MrDoritos/Wearable/dpad.png

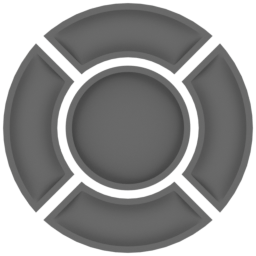
dpad.png
