MrDoritos/Wearable/dpad_arrow.png

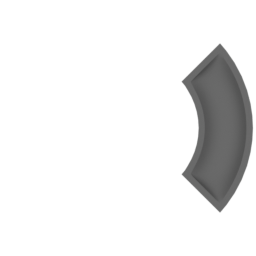
dpad_arrow.png
