MrDoritos/Wearable/dpad_enter.png

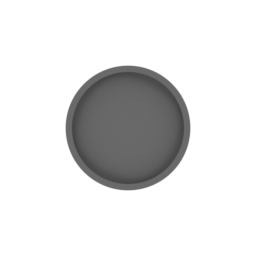
dpad_enter.png
