MrDoritos/Wearable/font.png

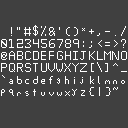
font.png
