MrDoritos/Wearable/fonts/fixedsys-excelsior-301.ttf_8x8.png

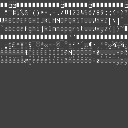
fonts/fixedsys-excelsior-301.ttf_8x8.png
