MrDoritos/Wearable/fonts/fixedsys-excelsior-301.ttf_8x14_fixed.png

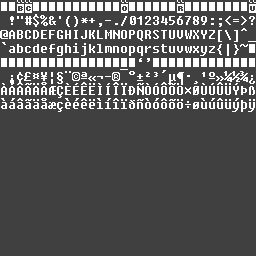
fonts/fixedsys-excelsior-301.ttf_8x14_fixed.png
