MrDoritos/Wearable/fonts/fixedsys-excelsior-301.ttf_12x12.png

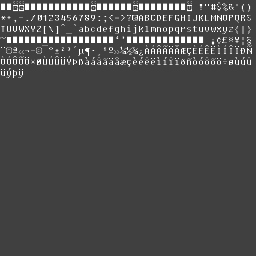
fonts/fixedsys-excelsior-301.ttf_12x12.png
