MrDoritos/Wearable/fonts/fixedsys-excelsior-301.ttf_12x16.png

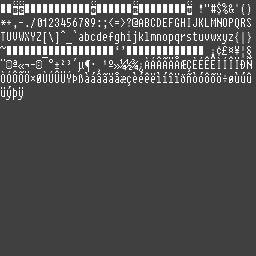
fonts/fixedsys-excelsior-301.ttf_12x16.png
