MrDoritos/Wearable/fonts/fixedsys-excelsior-301.ttf_14x16.png

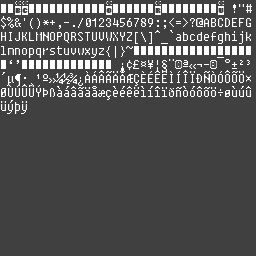
fonts/fixedsys-excelsior-301.ttf_14x16.png
