MrDoritos/Wearable/fonts/fixedsys-excelsior-301.ttf_16x16.png

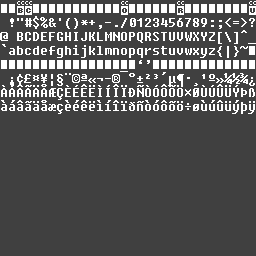
fonts/fixedsys-excelsior-301.ttf_16x16.png
