MrDoritos/Wearable/fonts/Perfect DOS VGA 437 Win.ttf_12x12.png

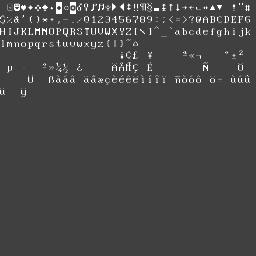
fonts/Perfect DOS VGA 437 Win.ttf_12x12.png
