MrDoritos/Wearable/fonts/Perfect DOS VGA 437 Win.ttf_16x16.png

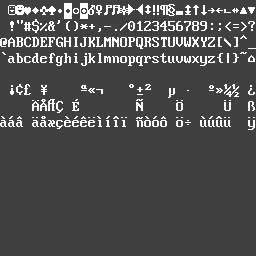
fonts/Perfect DOS VGA 437 Win.ttf_16x16.png
