MrDoritos/Wearable/fonts/Px437_DOS-V_re_JPN12.ttf_8x12.png

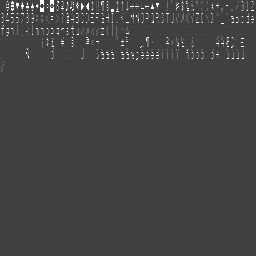
fonts/Px437_DOS-V_re_JPN12.ttf_8x12.png
