MrDoritos/Wearable/fonts/Px437_IBM_BIOS.ttf_7x7.png

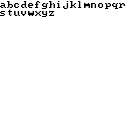
fonts/Px437_IBM_BIOS.ttf_7x7.png
