MrDoritos/Wearable/fonts/Px437_IBM_BIOS.ttf_8x12.png

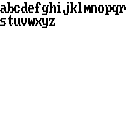
fonts/Px437_IBM_BIOS.ttf_8x12.png
