MrDoritos/Wearable/fonts/Px437_IBM_CGAthin.ttf_8x8.png

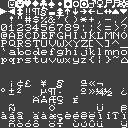
fonts/Px437_IBM_CGAthin.ttf_8x8.png
