MrDoritos/Wearable/fonts/Px437_IBM_Model3x_Alt1.ttf_8x16.png

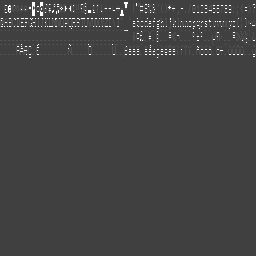
fonts/Px437_IBM_Model3x_Alt1.ttf_8x16.png
