MrDoritos/Wearable/fonts/Px437_IBM_Model3x_Alt1.ttf_16x16.png

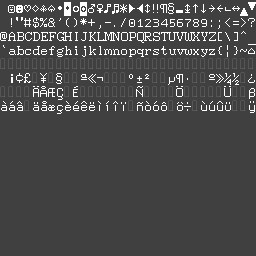
fonts/Px437_IBM_Model3x_Alt1.ttf_16x16.png
