MrDoritos/Wearable/fonts/Px437_IBM_VGA_9x16.ttf_8x16.png

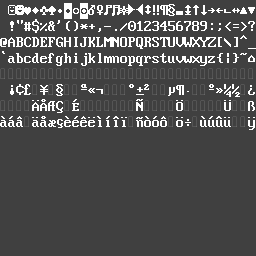
fonts/Px437_IBM_VGA_9x16.ttf_8x16.png
