MrDoritos/Wearable/fonts/raster.ttf_6x12.png

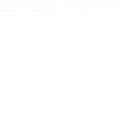
fonts/raster.ttf_6x12.png
