MrDoritos/Wearable/fonts/raster.ttf_8x8.png

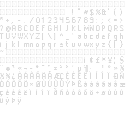
fonts/raster.ttf_8x8.png
