MrDoritos/Wearable/fonts/raster.ttf_12x16.png

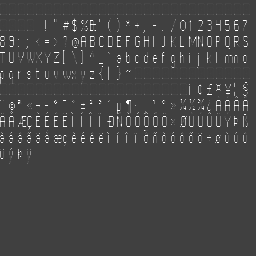
fonts/raster.ttf_12x16.png
