MrDoritos/Wearable/fonts/raster.ttf_16x12.png

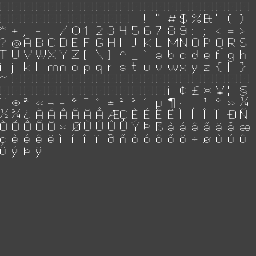
fonts/raster.ttf_16x12.png
