MrDoritos/Wearable/fonts/raster.ttf_16x16.png

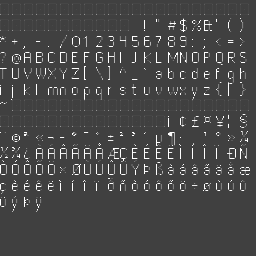
fonts/raster.ttf_16x16.png
