MrDoritos/Wearable/fonts/raster.ttf_20x16.png

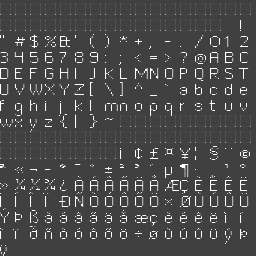
fonts/raster.ttf_20x16.png
