MrDoritos/Wearable/fonts/raster.ttf_24x16.png

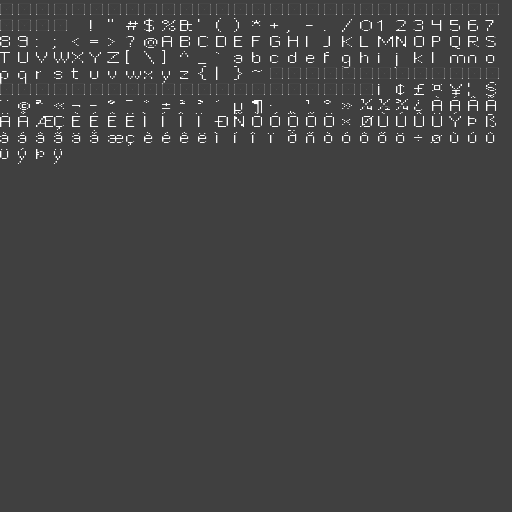
fonts/raster.ttf_24x16.png
