MrDoritos/Wearable/layout3.png

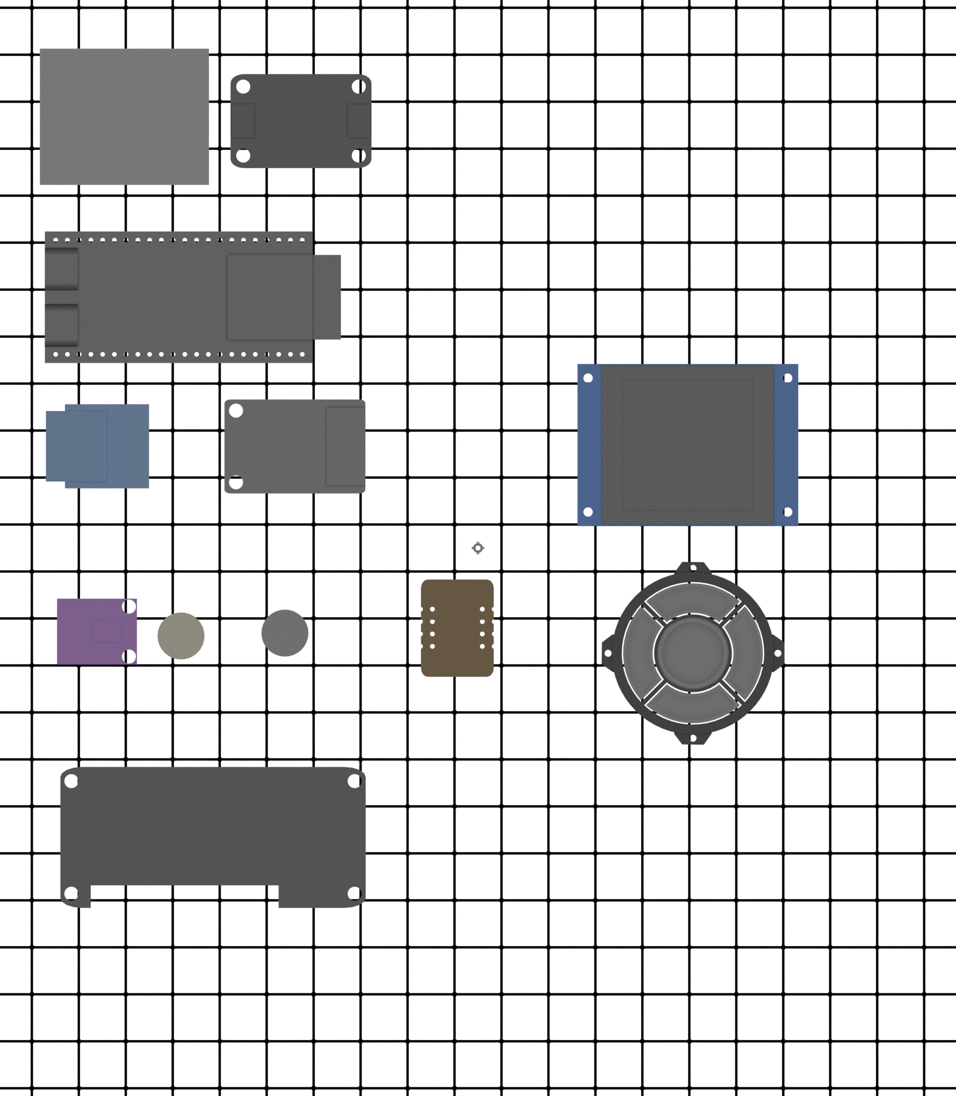
layout3.png
