MrDoritos/Wearable/layout.png

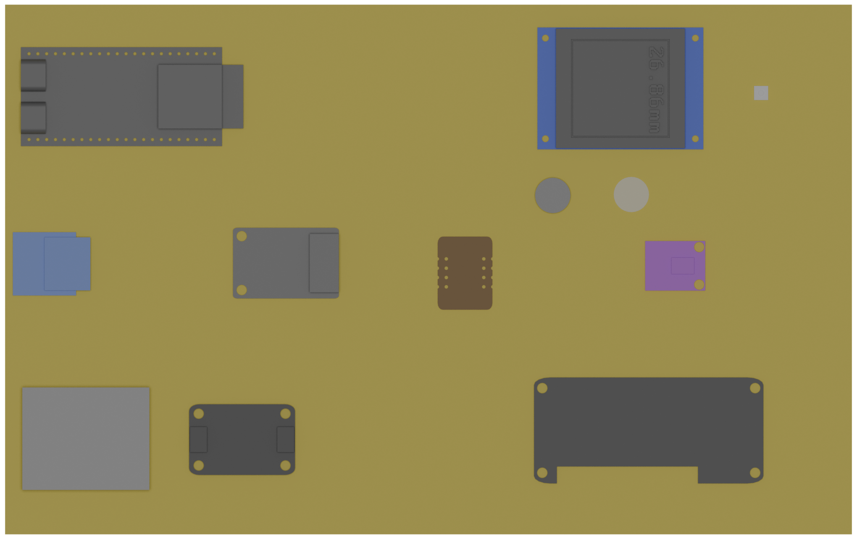
layout.png
