MrDoritos/Wearable/Pics/51+UH7-mXzL._SL1100_.jpg

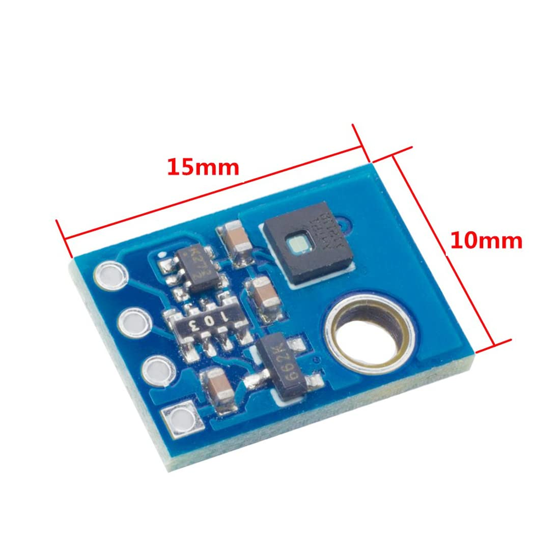
Pics/51+UH7-mXzL._SL1100_.jpg
