MrDoritos/Wearable/Pics/51AXbPtVahL._SL1200_.jpg

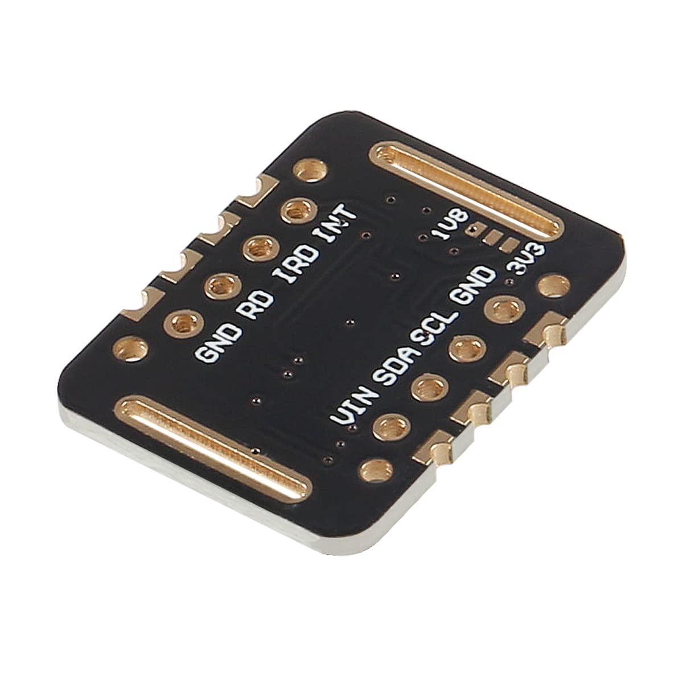
Pics/51AXbPtVahL._SL1200_.jpg
