MrDoritos/Wearable/Pics/51Op+VarA2L._SL1100_.jpg

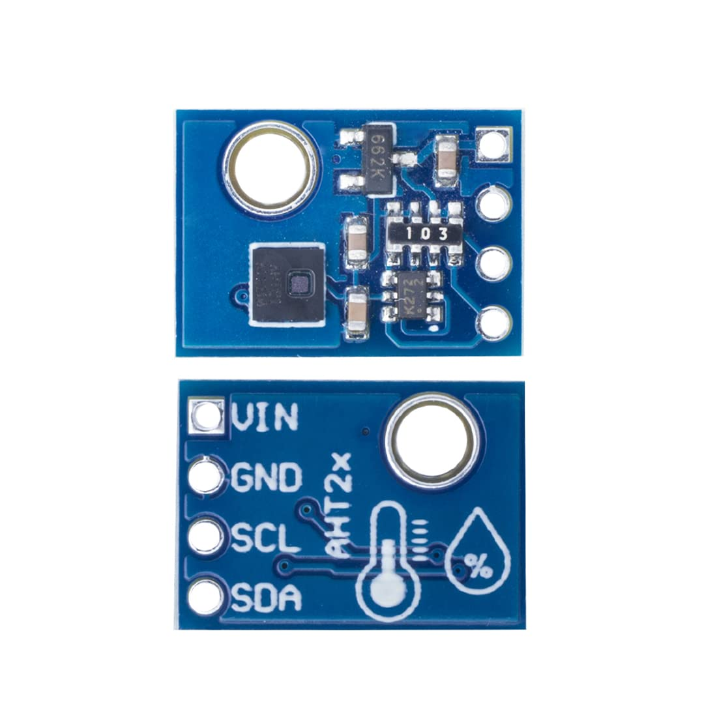
Pics/51Op+VarA2L._SL1100_.jpg
