MrDoritos/Wearable/Pics/51P6r7VXNBL._SL1000_.jpg

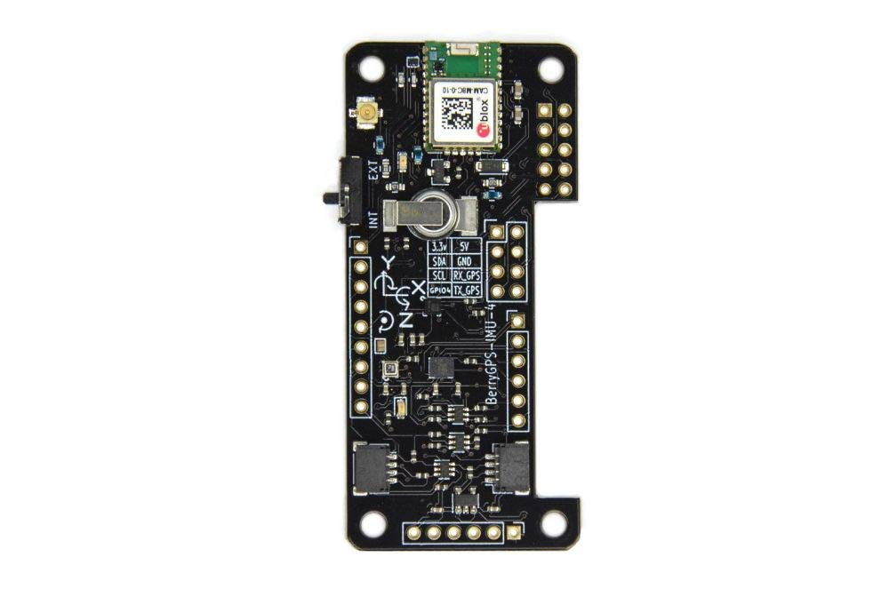
Pics/51P6r7VXNBL._SL1000_.jpg
