MrDoritos/Wearable/Pics/51W31oze62L._SL1200_.jpg

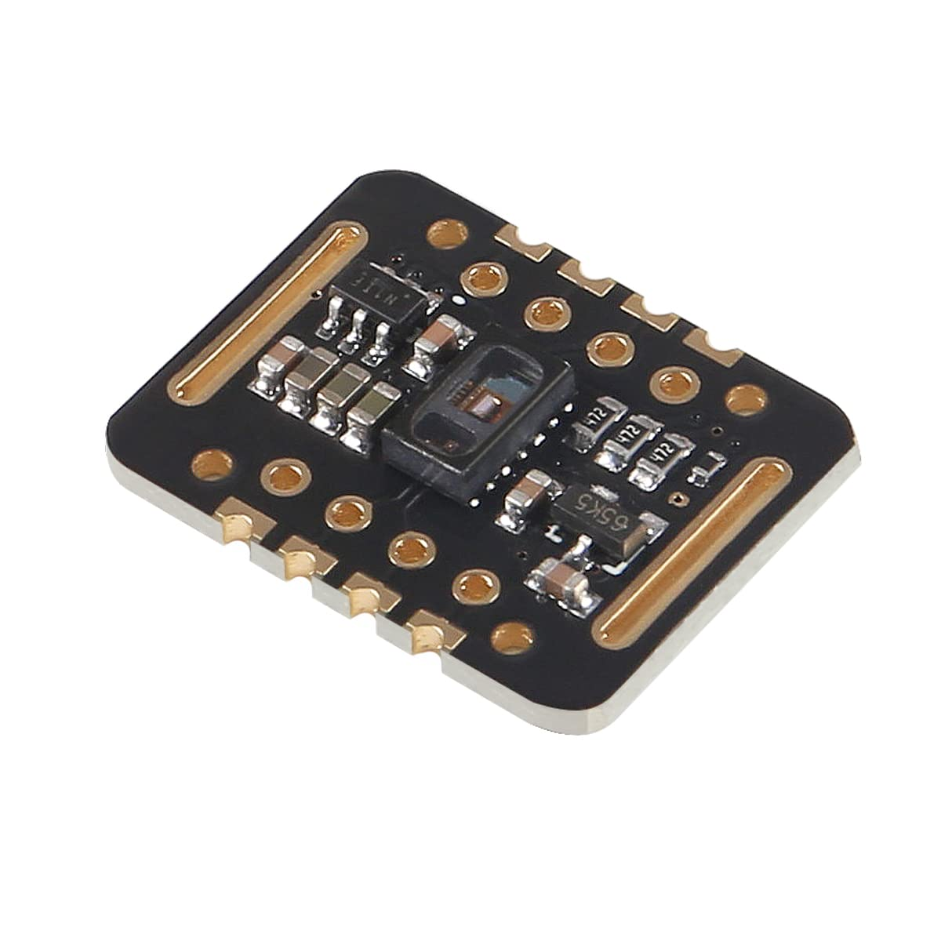
Pics/51W31oze62L._SL1200_.jpg
