MrDoritos/Wearable/Pics/51ZjLzfTUjL.jpg

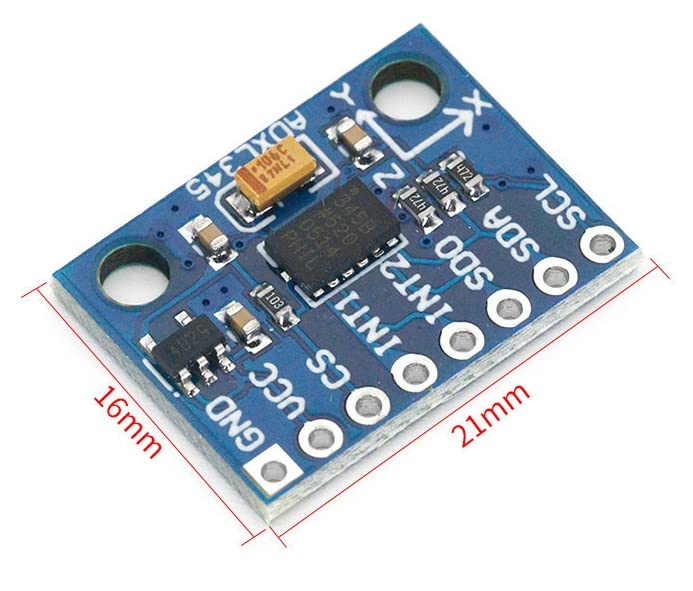
Pics/51ZjLzfTUjL.jpg
