MrDoritos/Wearable/Pics/61DWyjEP5hL._AC_SL1000_.jpg

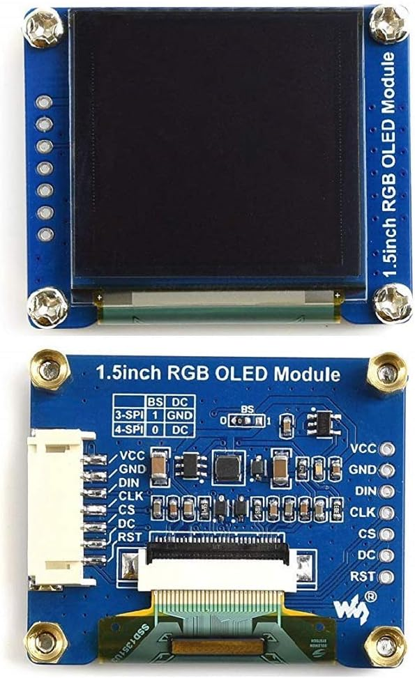
Pics/61DWyjEP5hL._AC_SL1000_.jpg
