MrDoritos/Wearable/Pics/61G-zMD8dRL._SL1000_.jpg

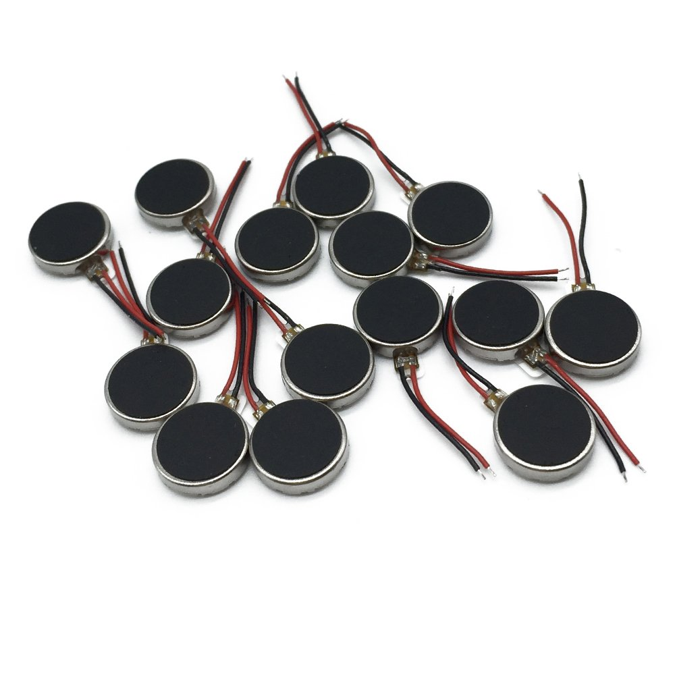
Pics/61G-zMD8dRL._SL1000_.jpg
