MrDoritos/Wearable/Pics/61ibA389aeL._AC_SL1500_.jpg

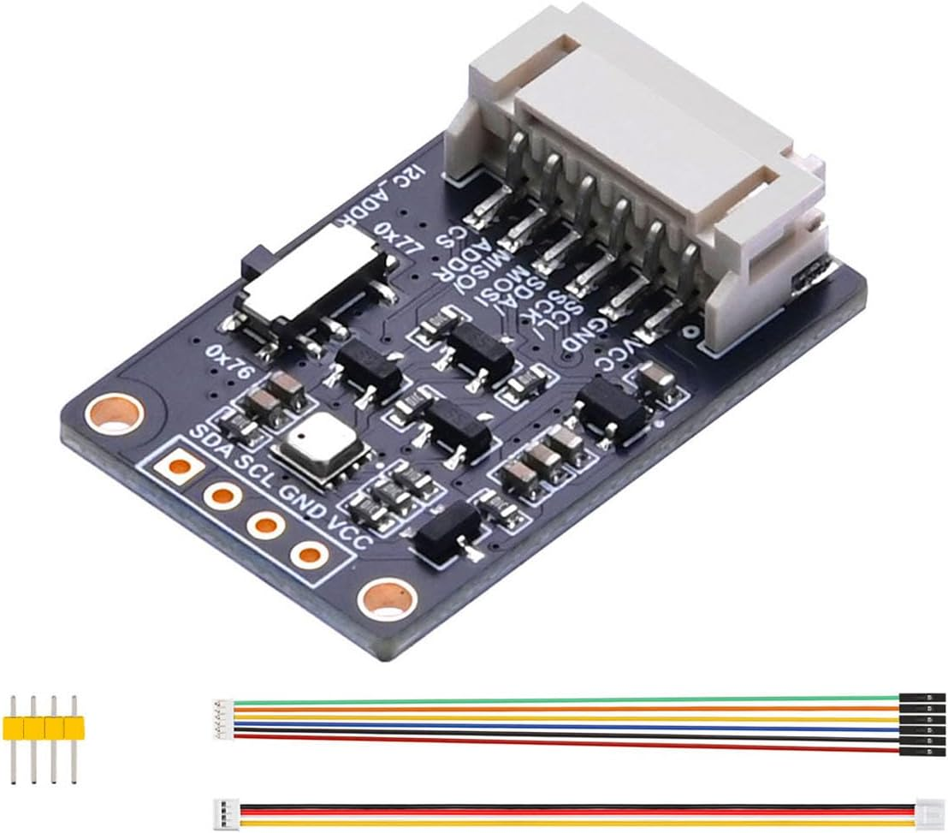
Pics/61ibA389aeL._AC_SL1500_.jpg
