MrDoritos/Wearable/Pics/61LNeiGi+DL._SL1200_.jpg

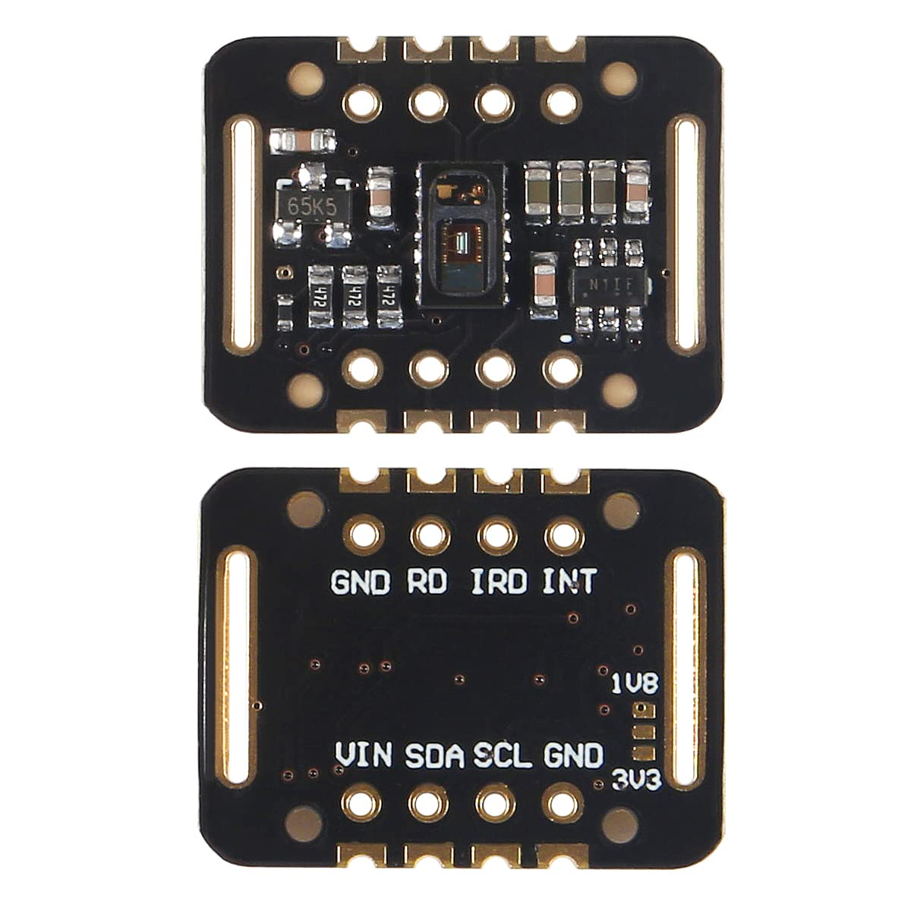
Pics/61LNeiGi+DL._SL1200_.jpg
