MrDoritos/Wearable/Pics/61Ofmry2-IL._SL1000_.jpg

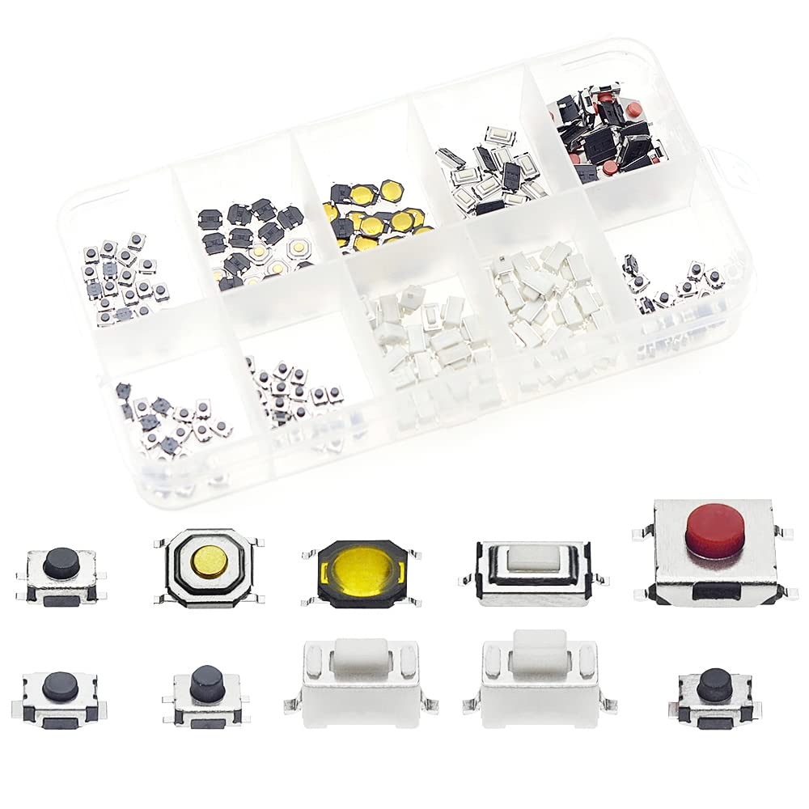
Pics/61Ofmry2-IL._SL1000_.jpg
