MrDoritos/Wearable/Pics/61Oh5a2cU0L._AC_SL1200_.jpg

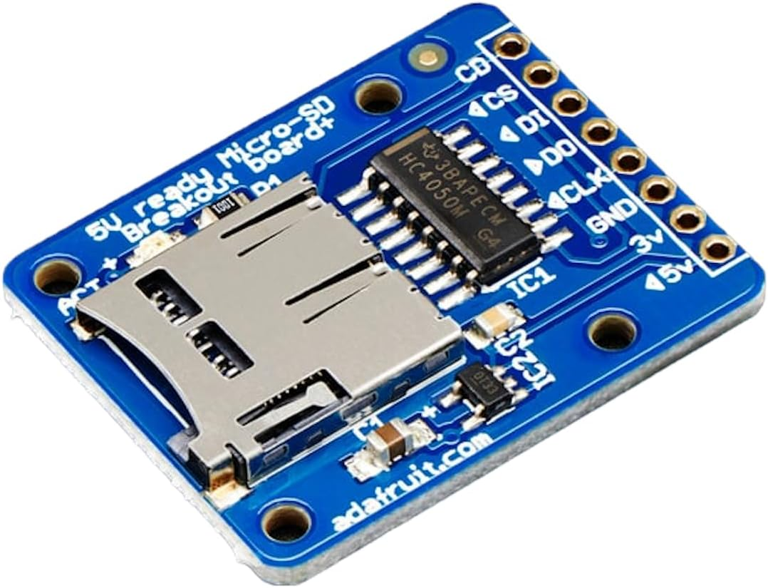
Pics/61Oh5a2cU0L._AC_SL1200_.jpg
