MrDoritos/Wearable/Pics/61qT42ub8qL._SL1200_.jpg

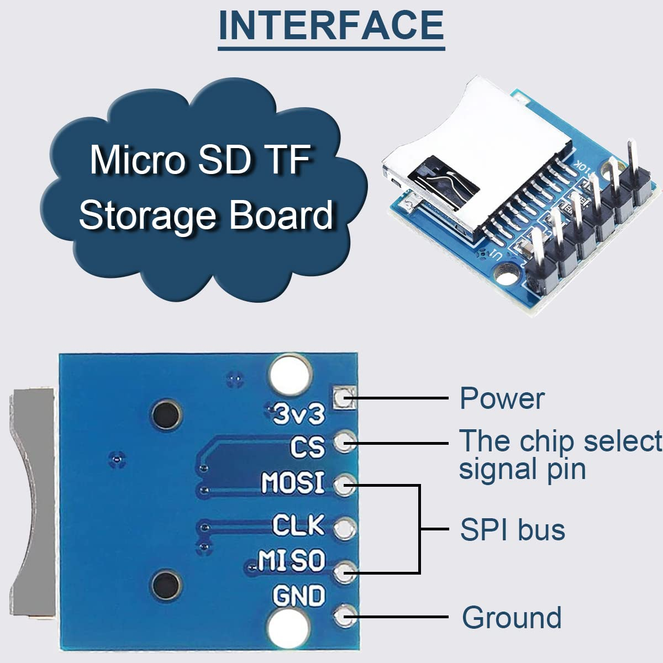
Pics/61qT42ub8qL._SL1200_.jpg
