MrDoritos/Wearable/Pics/61SEPn4aGYL._SL1100_.jpg

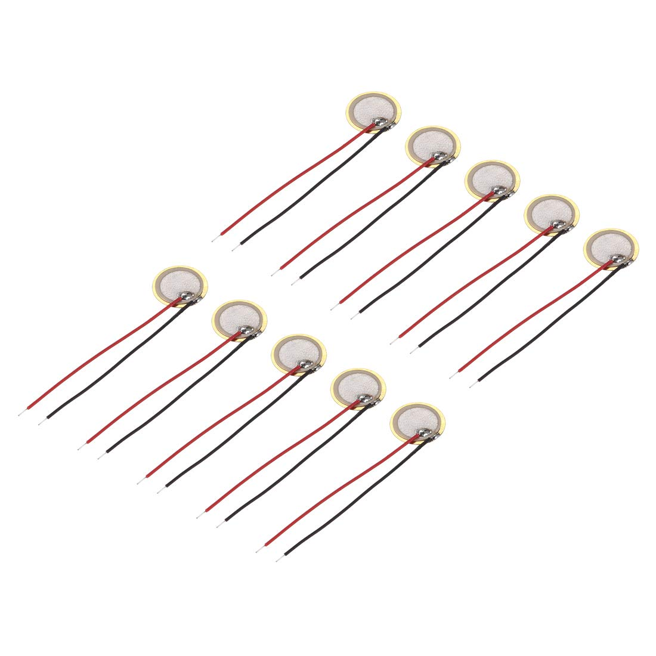
Pics/61SEPn4aGYL._SL1100_.jpg
