MrDoritos/Wearable/Pics/61SvwQWat1L._AC_SL1500_.jpg

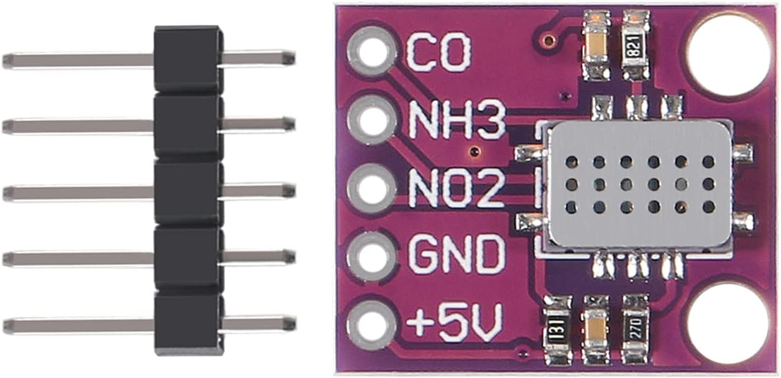
Pics/61SvwQWat1L._AC_SL1500_.jpg
