MrDoritos/Wearable/Pics/71bgBU8mavL._AC_SL1500_.jpg

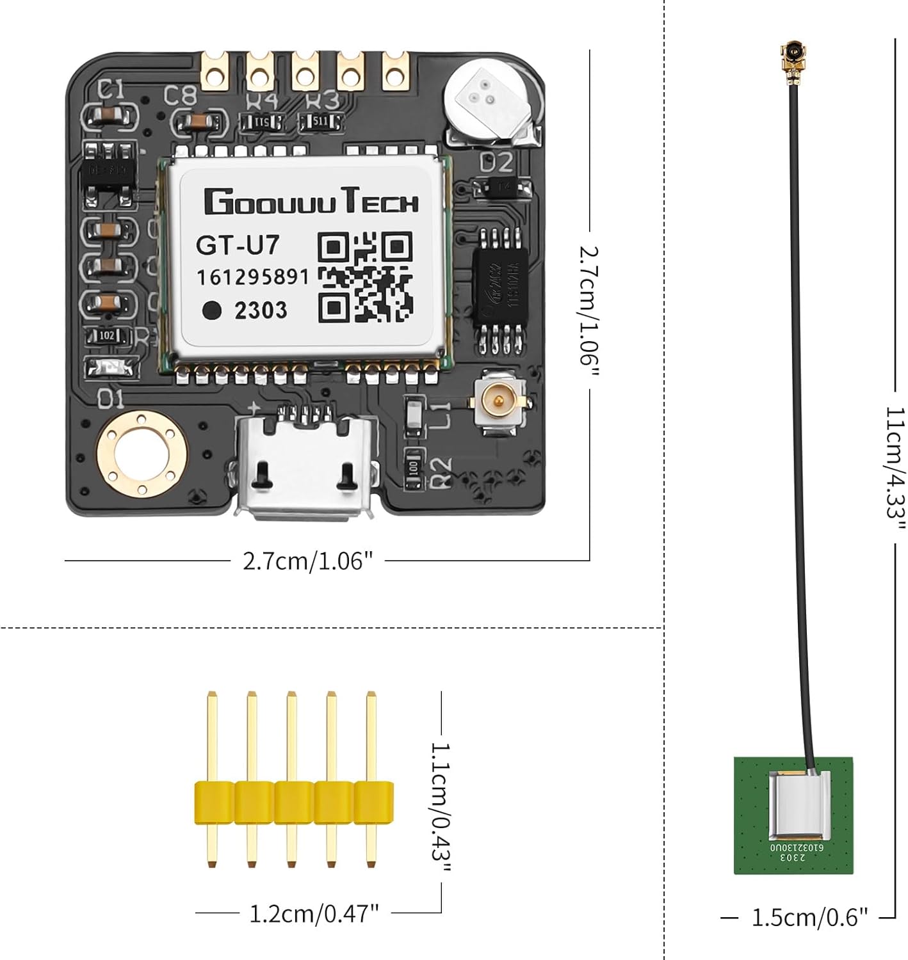
Pics/71bgBU8mavL._AC_SL1500_.jpg
