MrDoritos/Wearable/Pics/71tm7mbUd7L._AC_SL1500_.jpg

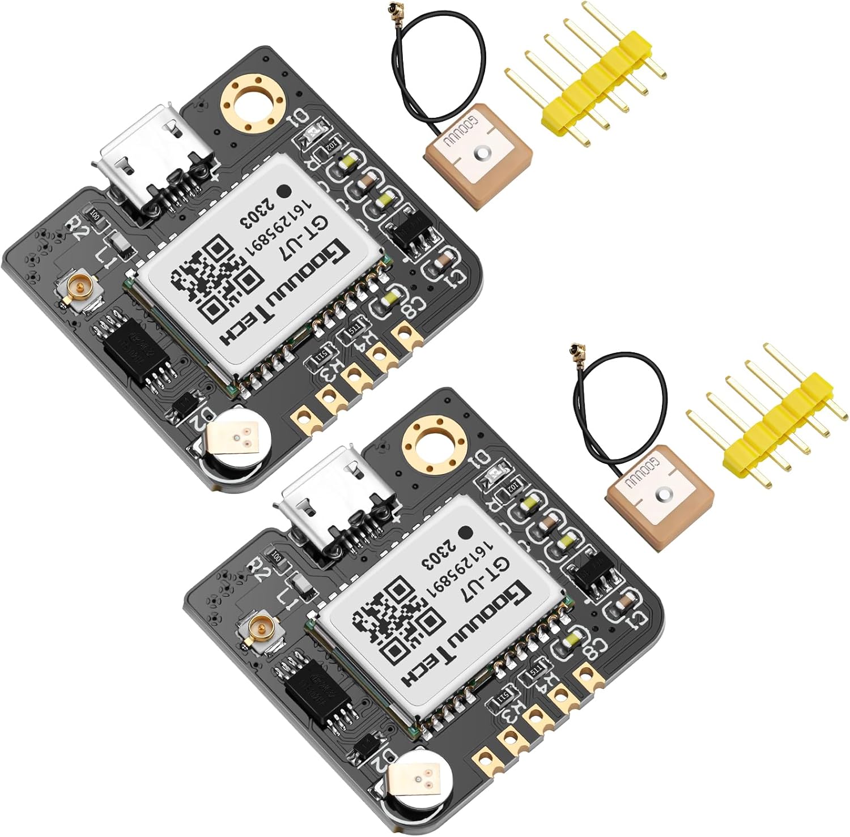
Pics/71tm7mbUd7L._AC_SL1500_.jpg
