MrDoritos/Wearable/Pics/71tysou55pL._SL1500_.jpg

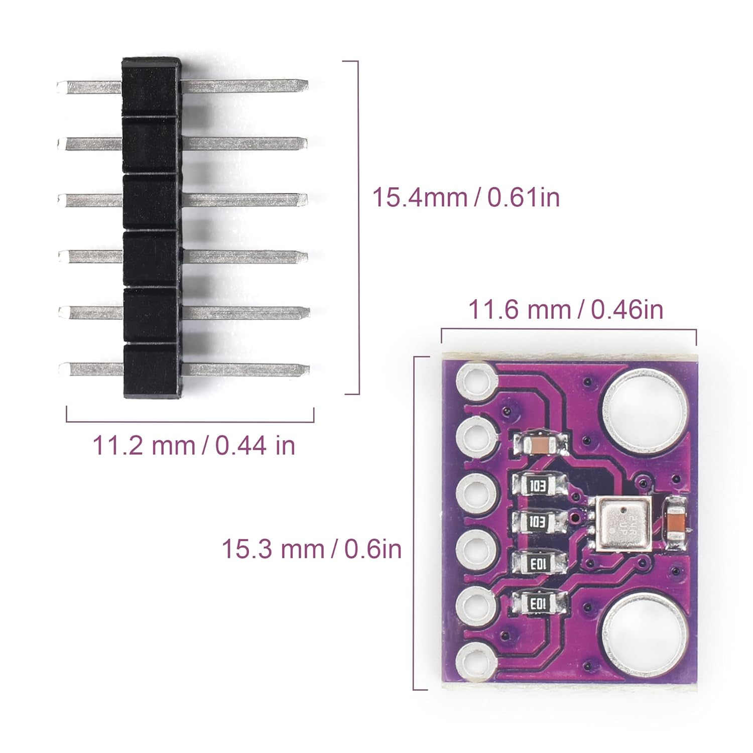
Pics/71tysou55pL._SL1500_.jpg
