MrDoritos/Wearable/Pics/71Z4uBD5LkL._SL1500_.jpg

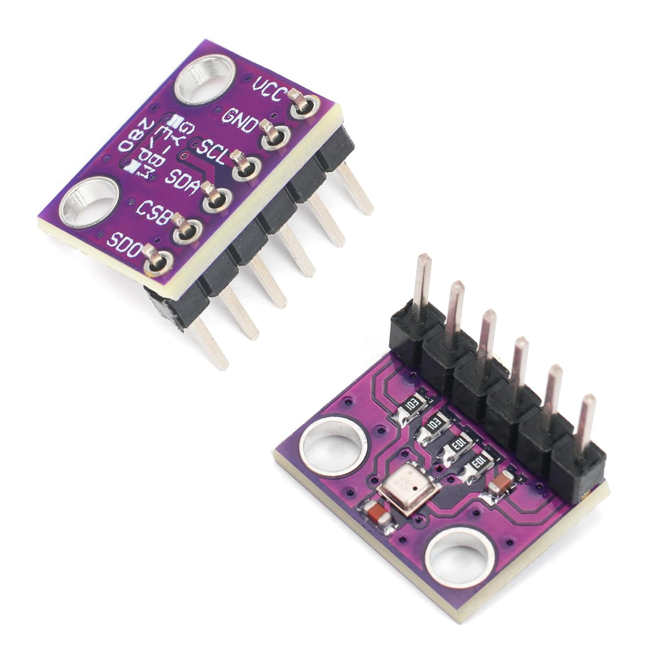
Pics/71Z4uBD5LkL._SL1500_.jpg
