MrDoritos/Wearable/Pics/81cLeyj0tDL._AC_SL1200_.jpg

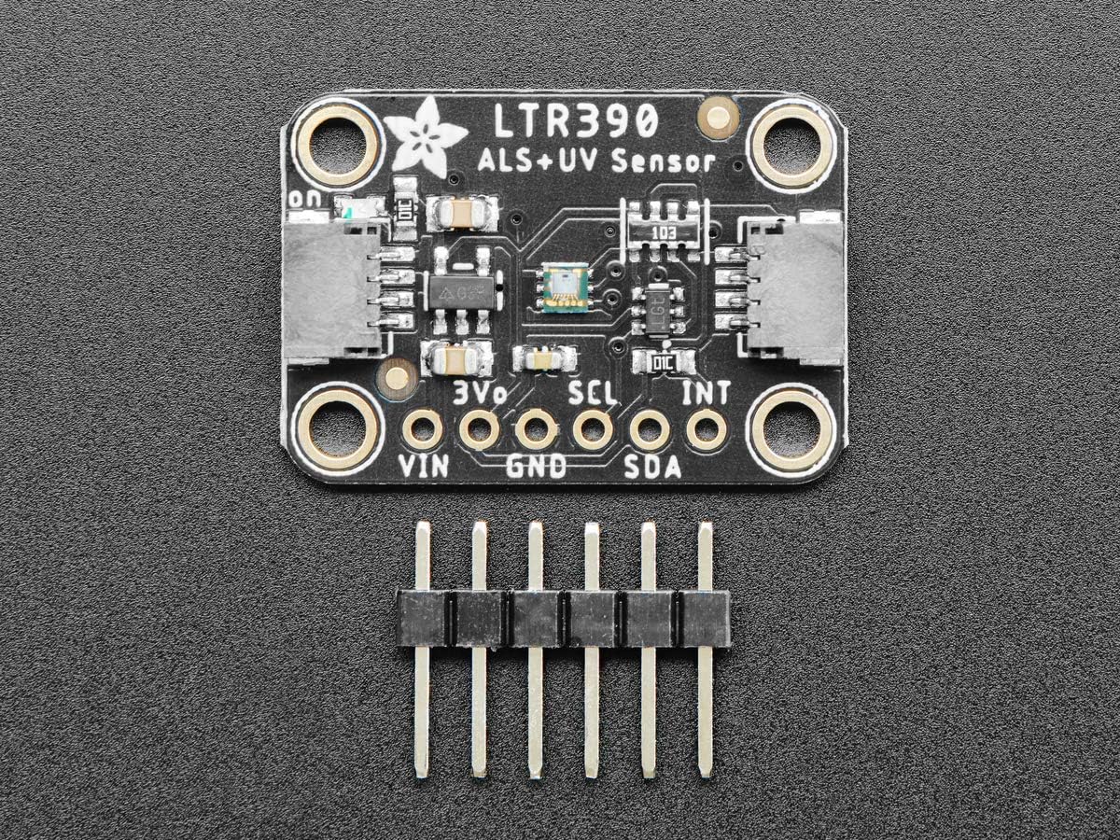
Pics/81cLeyj0tDL._AC_SL1200_.jpg
