MrDoritos/Wearable/Pics/258-03.jpg

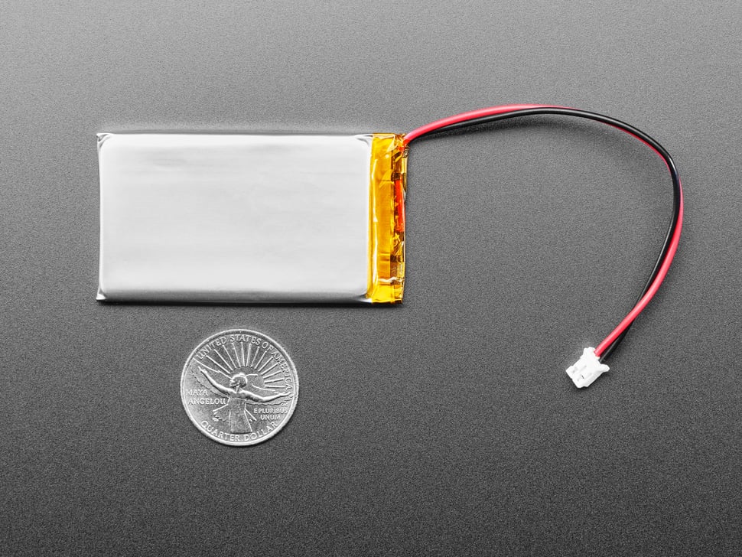
Pics/258-03.jpg
