MrDoritos/Wearable/Pics/612WX71x2jS._SL1500_.jpg

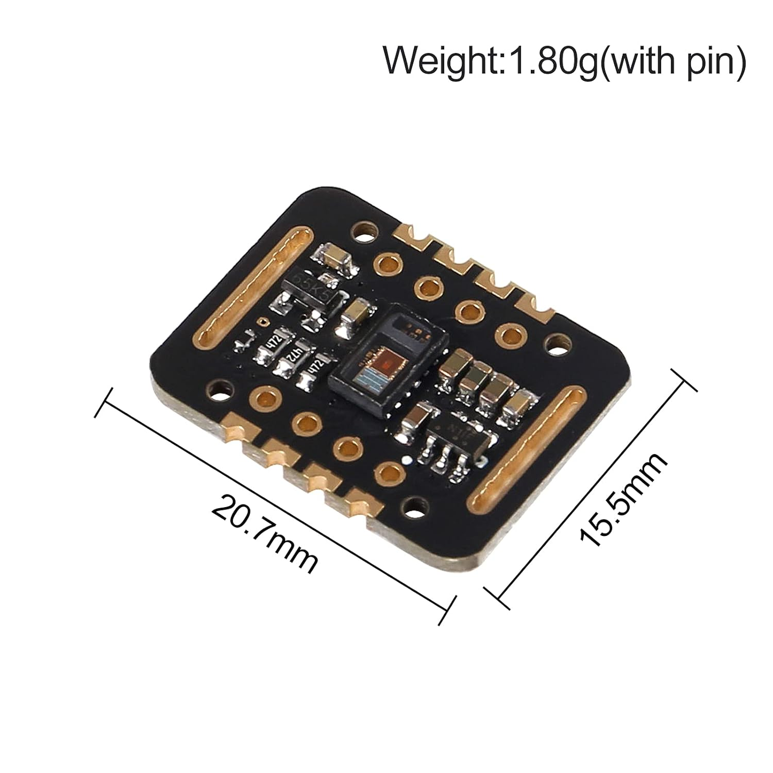
Pics/612WX71x2jS._SL1500_.jpg
