MrDoritos/Wearable/Pics/617YnlqChTL._AC_SL1200_.jpg

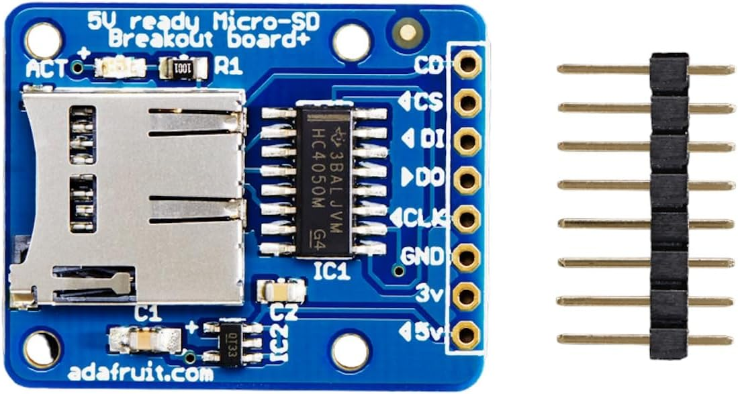
Pics/617YnlqChTL._AC_SL1200_.jpg
