MrDoritos/Wearable/Pics/1578-05.jpg

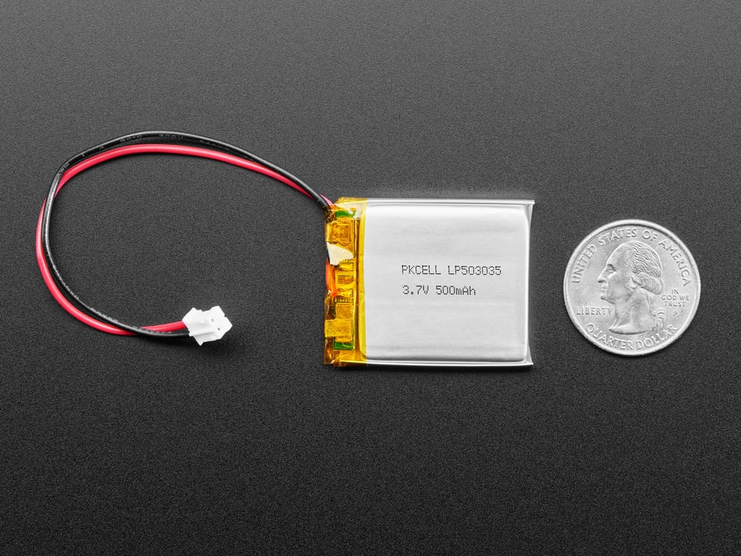
Pics/1578-05.jpg
