MrDoritos/Wearable/Pics/2491-05.jpg

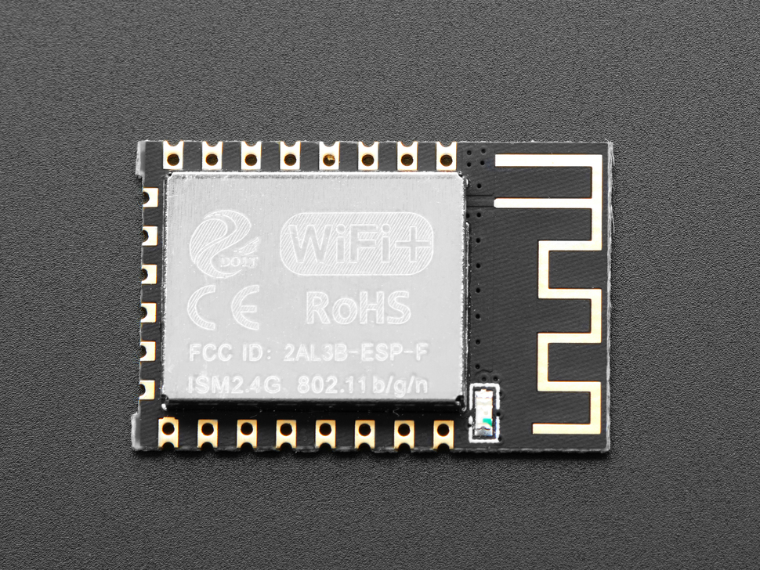
Pics/2491-05.jpg
