MrDoritos/Wearable/Pics/fabric/Ice Fabrics Nylon Spandex Fabric by The Yard - 60_ Wide Spandex Swimwear Fabric - 4 Way Stretch for Active Wear 91QMyVfP-5L._AC_SL1500_.jpg

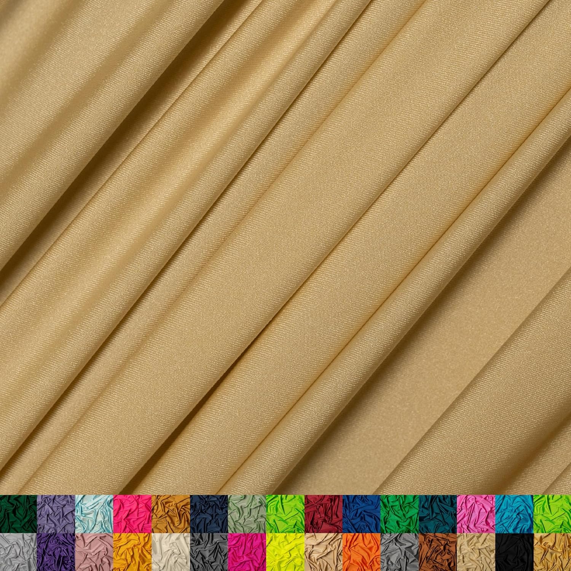
Pics/fabric/Ice Fabrics Nylon Spandex Fabric by The Yard - 60_ Wide Spandex Swimwear Fabric - 4 Way Stretch for Active Wear 91QMyVfP-5L._AC_SL1500_.jpg
