MrDoritos/Wearable/Pics/fabric/Pico Textiles 1 Yard - Black Polyester Micro Mesh Jersey Fabric 81RQ++7rJ6L._AC_SL1500_.jpg

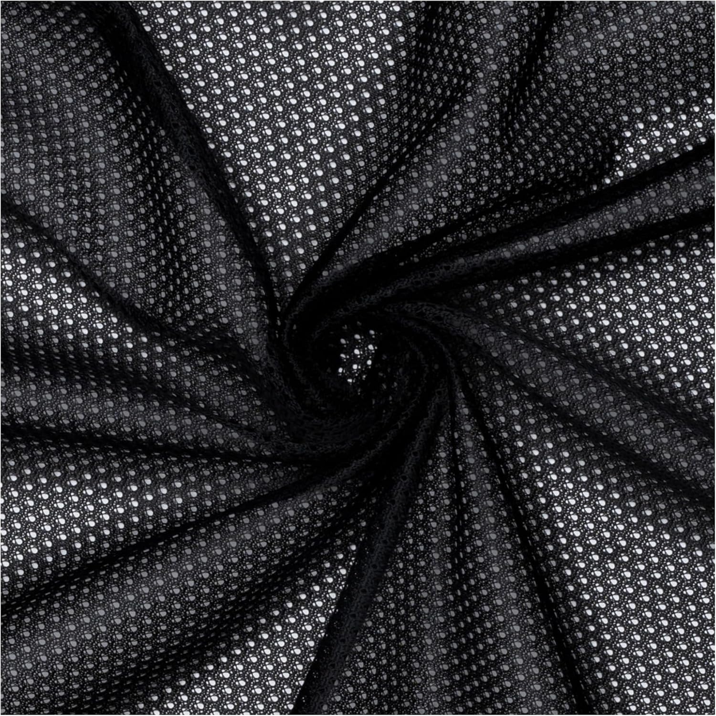
Pics/fabric/Pico Textiles 1 Yard - Black Polyester Micro Mesh Jersey Fabric 81RQ++7rJ6L._AC_SL1500_.jpg
