MrDoritos/Wearable/Pics/fabric/Stylish FABRIC 60" Wide Rayon Spandex Jersey Knit Fabric by The Yard-4-Way Stretch, 200GSM, Medium Weight-Soft & Breathable-Apparel 91u+m-NSM8L._AC_SL1500_.jpg

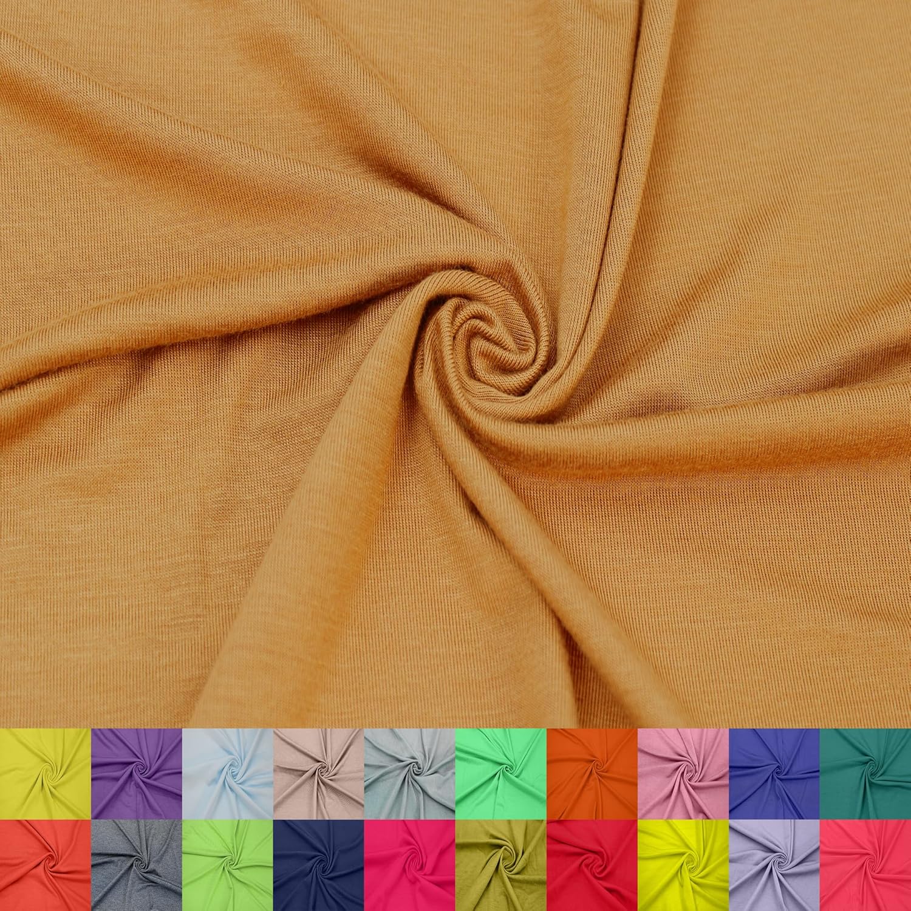
Pics/fabric/Stylish FABRIC 60" Wide Rayon Spandex Jersey Knit Fabric by The Yard-4-Way Stretch, 200GSM, Medium Weight-Soft & Breathable-Apparel 91u+m-NSM8L._AC_SL1500_.jpg
