MrDoritos/Wearable/Pics/GOME.uviecclimyear_lr.gif

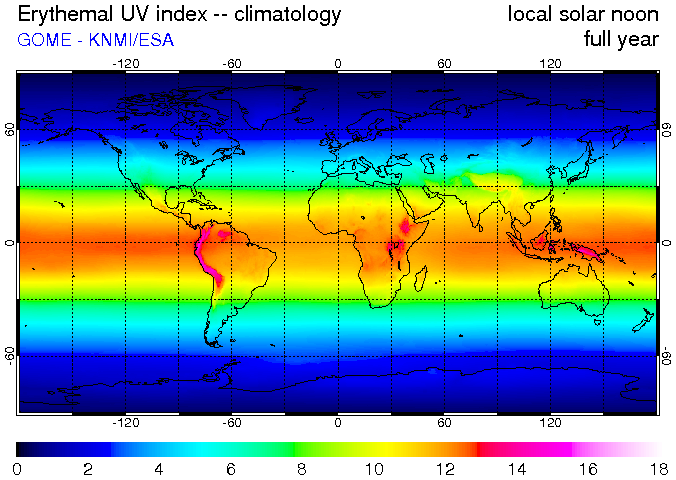
Pics/GOME.uviecclimyear_lr.gif
