MrDoritos/Wearable/Pics/piezo.jpeg

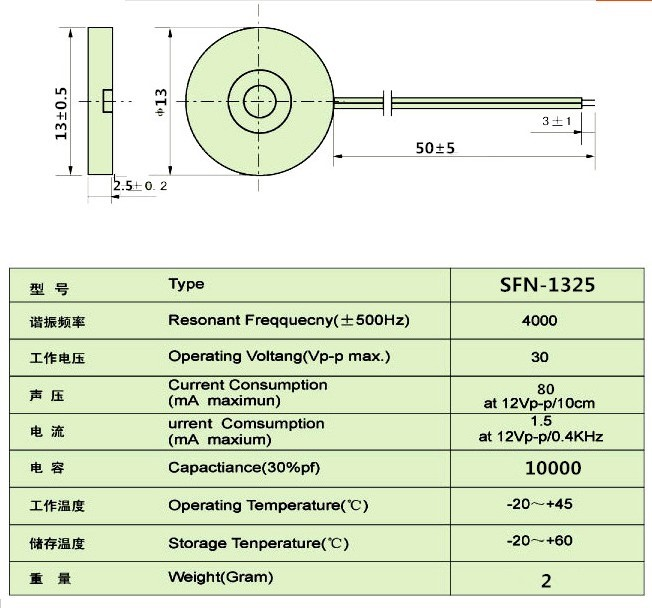
Pics/piezo.jpeg
