MrDoritos/Wearable/Pics/REA128128A-contour-drawing.jpg

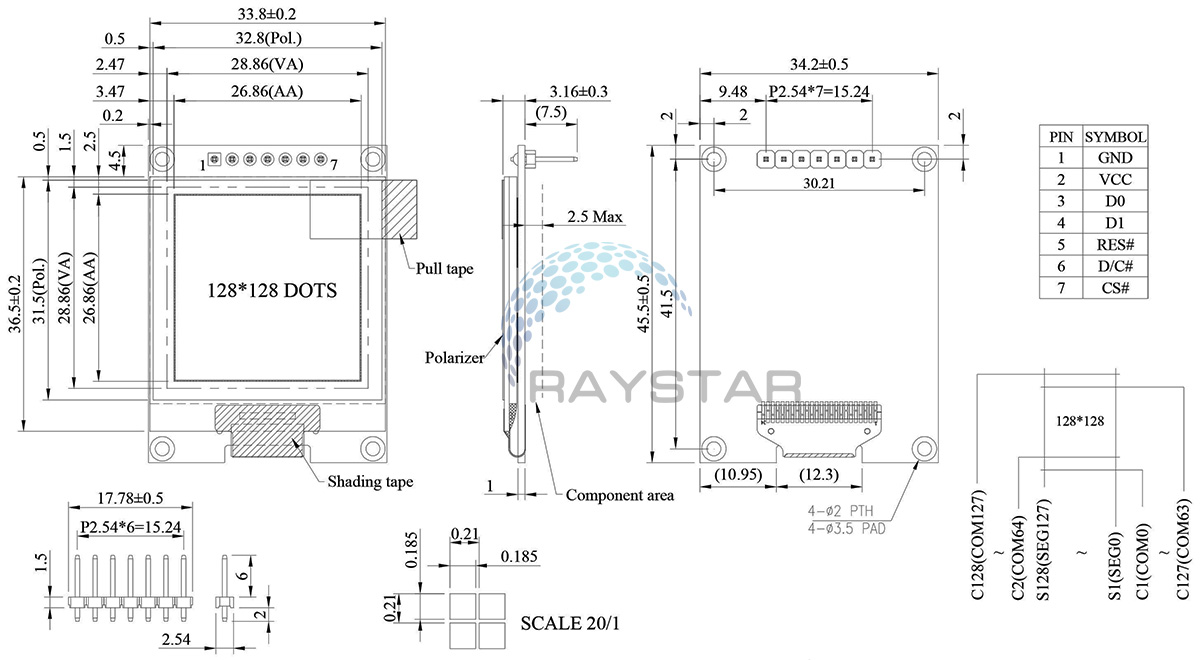
Pics/REA128128A-contour-drawing.jpg
