MrDoritos/Wearable/Pics/Screenshot 2025-08-01 at 20-14-23 Ultraviolet index - Wikipedia.png

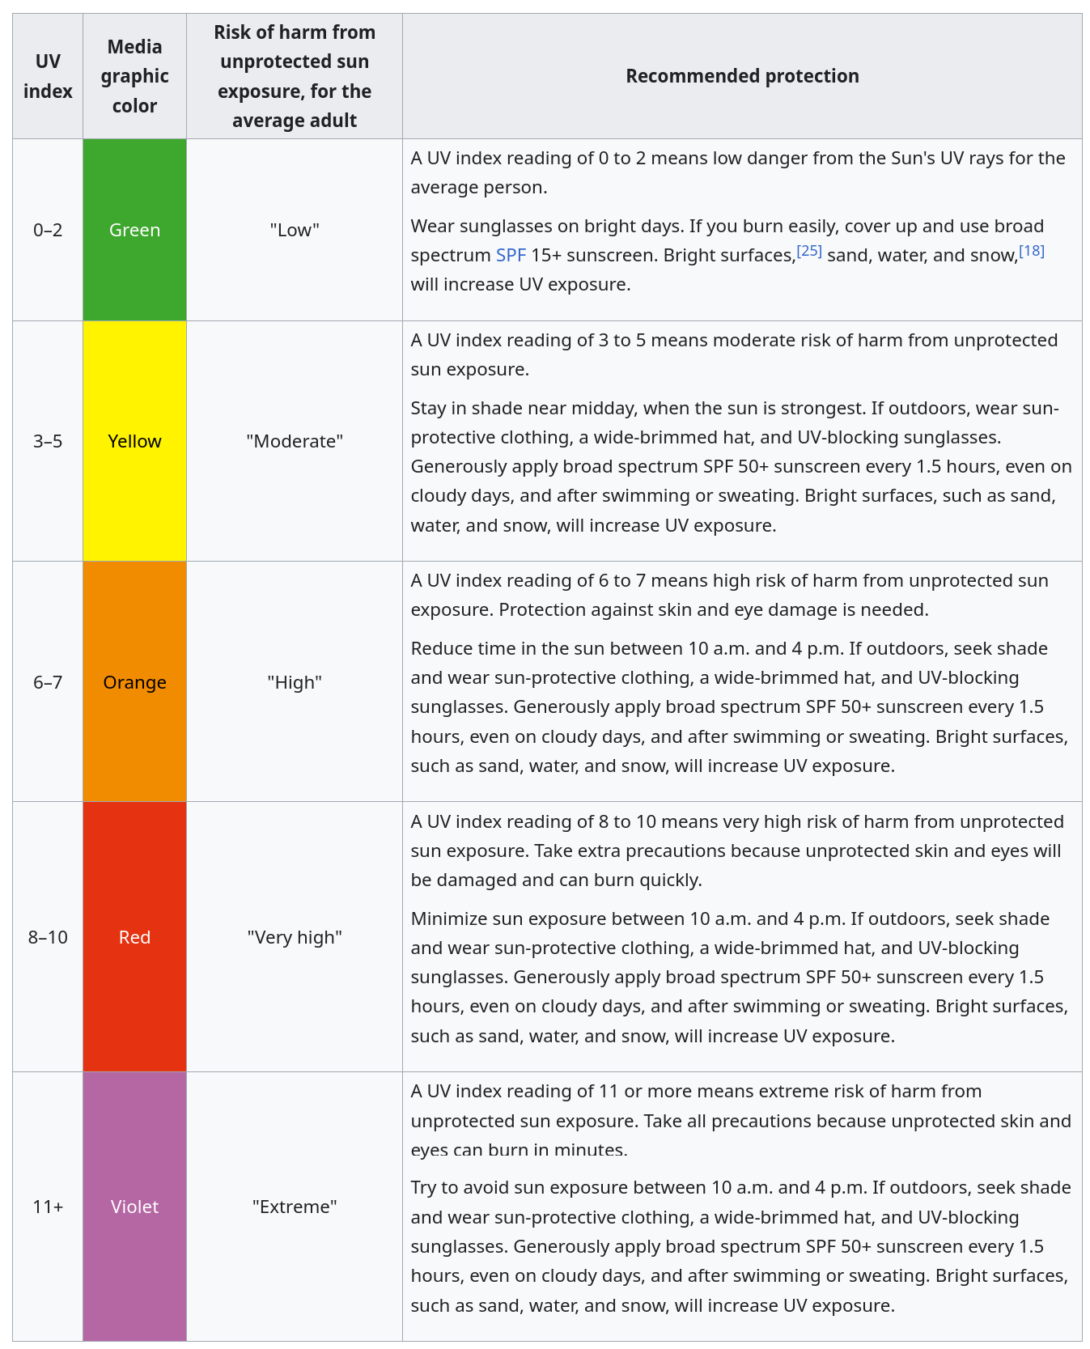
Pics/Screenshot 2025-08-01 at 20-14-23 Ultraviolet index - Wikipedia.png
