MrDoritos/Wearable/Pics/UV_Index_NYC.png

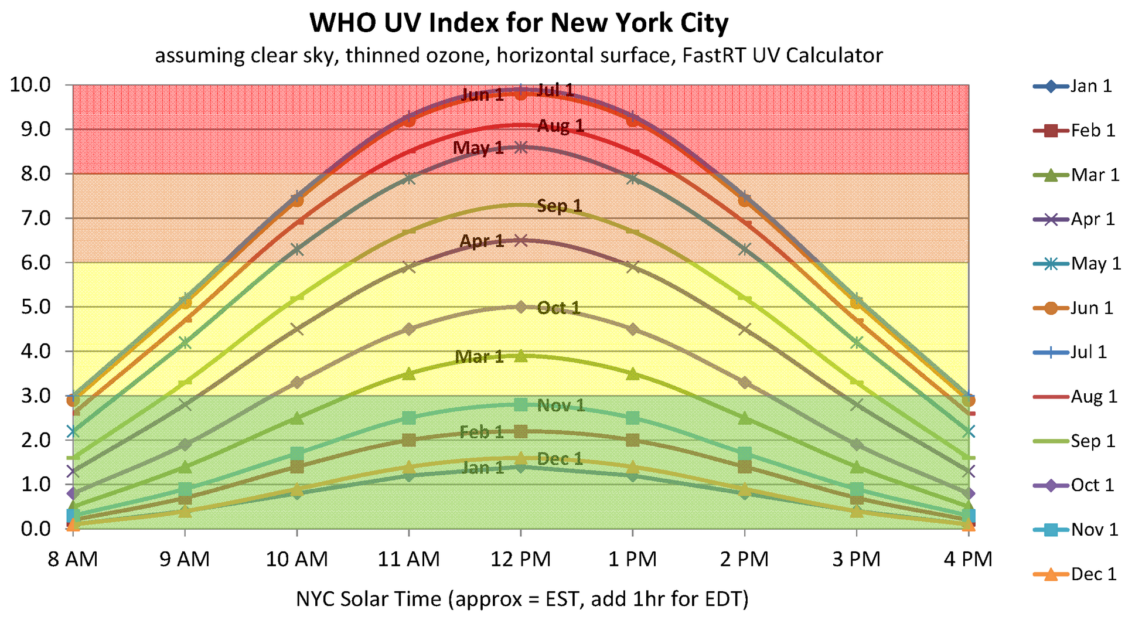
Pics/UV_Index_NYC.png
