MrDoritos/Wearable/Pics/UVspectrum1.jpg

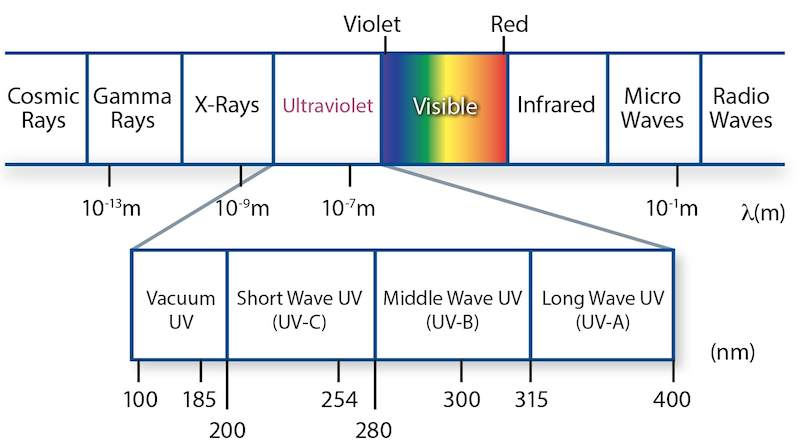
Pics/UVspectrum1.jpg
