MrDoritos/Wearable/textures.png

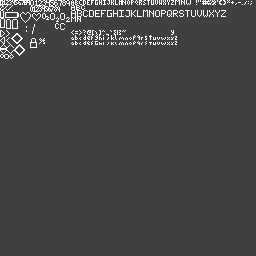
textures.png
