MrDoritos/Wearable/the_rock.png

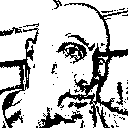
the_rock.png
