MrDoritos/Wearable/Pics/fabric/TinaKim Ribbing Fabric for Cuffs, Jacket Hoodies Waistbands Neckline Material 81t1N6D-ejL._AC_SL1500_.jpg

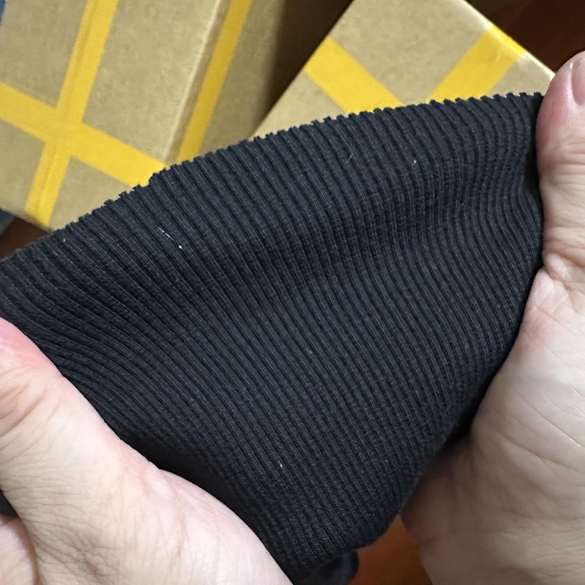
Pics/fabric/TinaKim Ribbing Fabric for Cuffs, Jacket Hoodies Waistbands Neckline Material 81t1N6D-ejL._AC_SL1500_.jpg
