MrDoritos/Wearable/stl/PartsLipo_500mAh.001.stl

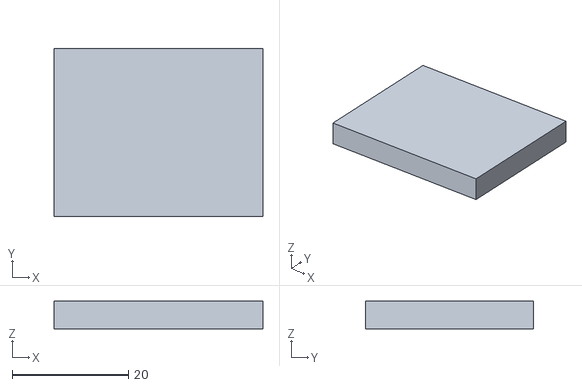
[picture p87: CAD file, 2025-07-22]
stl/PartsLipo_500mAh.001.stl
36.0 x 29.0 x 4.75
