MrDoritos/Wearable/stl/PartsMAX30102_PCB.001.stl

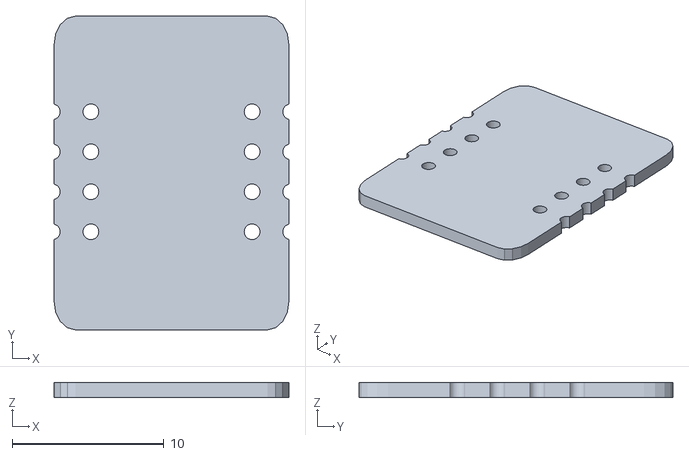
[picture p88: CAD file, 2025-07-22]
stl/PartsMAX30102_PCB.001.stl
15.5 x 20.7 x 0.969
