MrDoritos/Wearable/stl/PartsSD_card_PCB.001.stl

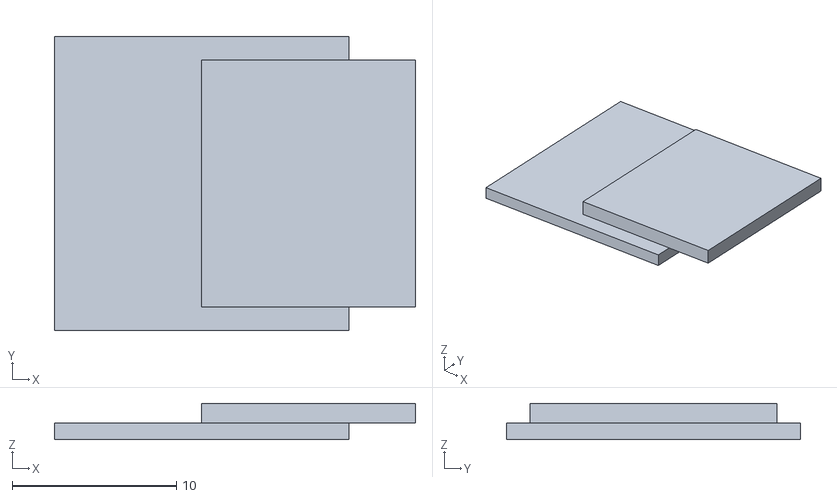
[picture p89: CAD file, 2025-07-22]
stl/PartsSD_card_PCB.001.stl
21.9 x 17.9 x 2.20
