MrDoritos/Wearable/stl/PartsBerryGPS-IMU_PCB.001.stl

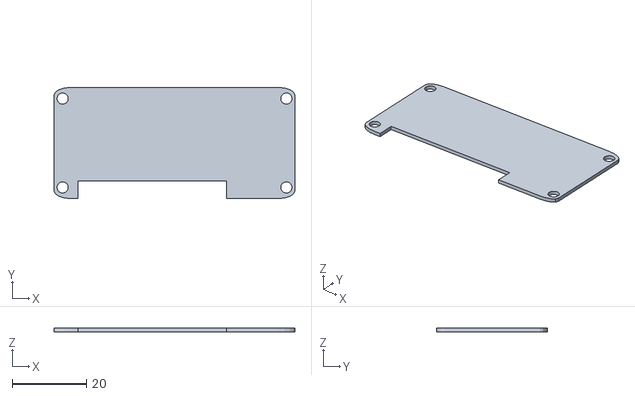
[picture p90: CAD file, 2025-07-22]
stl/PartsBerryGPS-IMU_PCB.001.stl
65.0 x 30.0 x 1.00
