MrDoritos/Wearable/stl/PartsLTR390-UV_PCB.001.stl

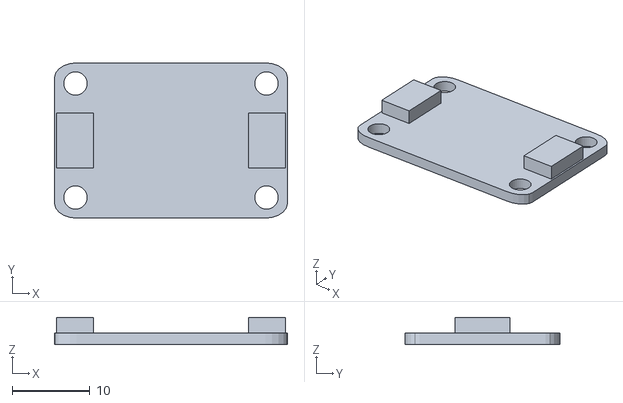
[picture p91: CAD file, 2025-07-22]
stl/PartsLTR390-UV_PCB.001.stl
30.0 x 20.0 x 3.50
