MrDoritos/Wearable/stl/PartsESP32_PCB.001.stl

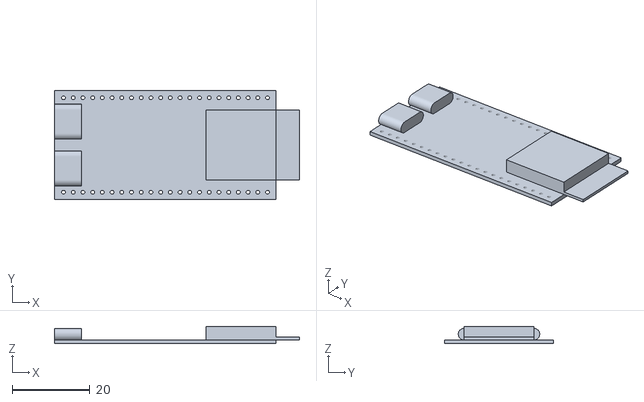
[picture p92: CAD file, 2025-07-22]
stl/PartsESP32_PCB.001.stl
63.0 x 28.0 x 4.50
