MrDoritos/Wearable/stl/PartsPiezo.001.stl

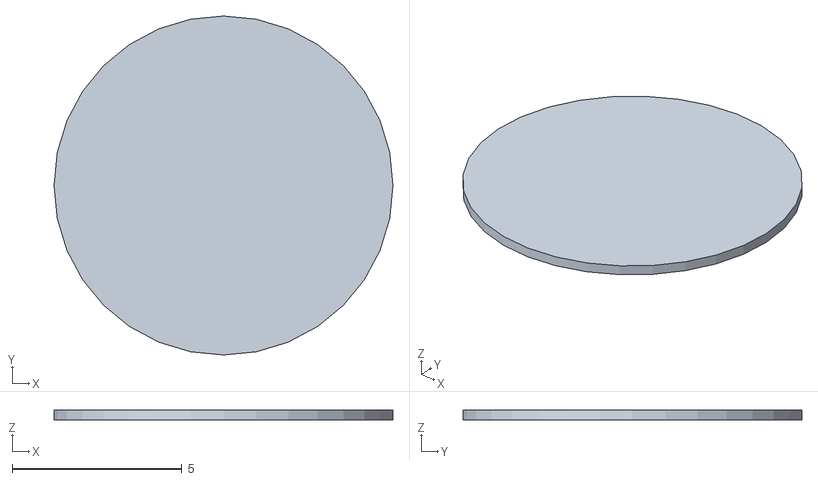
[picture p93: CAD file, 2025-07-22]
stl/PartsPiezo.001.stl
10.0 x 10.0 x 0.3
