MrDoritos/Wearable/stl/PartsMICS-6814_PCB.001.stl

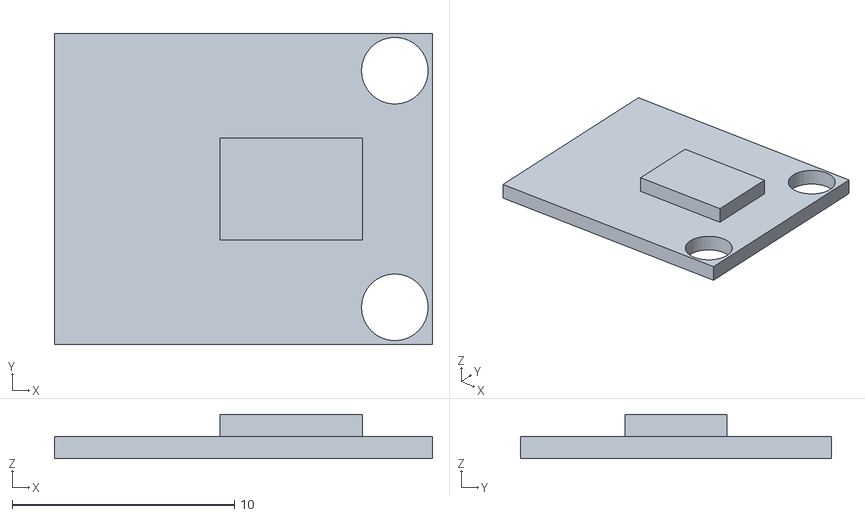
[picture p94: CAD file, 2025-07-22]
stl/PartsMICS-6814_PCB.001.stl
17.0 x 14.0 x 2.00
