MrDoritos/Wearable/stl/PartsHaptic_Motor.001.stl

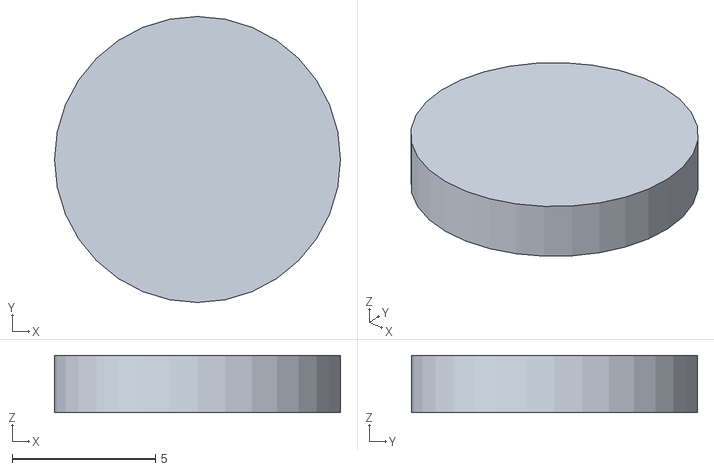
[picture p95: CAD file, 2025-07-22]
stl/PartsHaptic_Motor.001.stl
10.0 x 10.0 x 2.00
