MrDoritos/Wearable/stl/dpadbuttondemo.stl

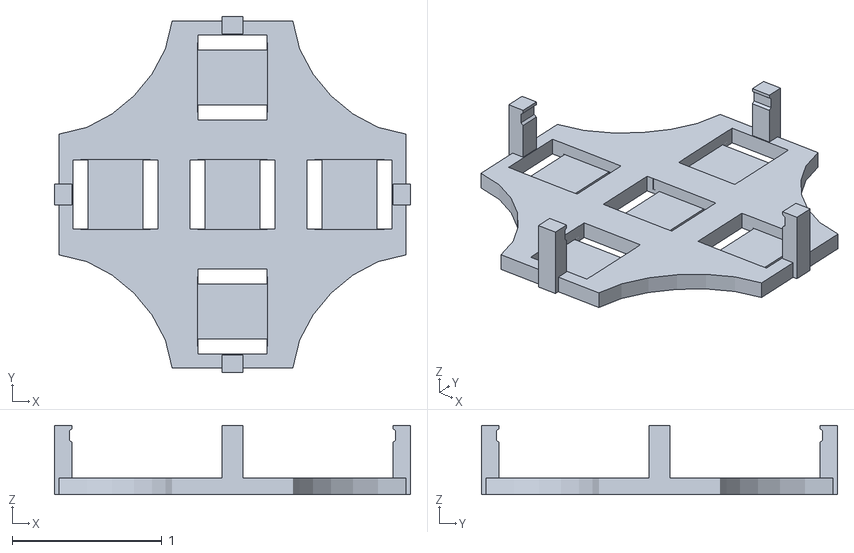
[picture p96: CAD file, 2025-07-07]
stl/dpadbuttondemo.stl
2.38 x 2.38 x 0.462
