MrDoritos/Wearable/stl/dpadring.3mf

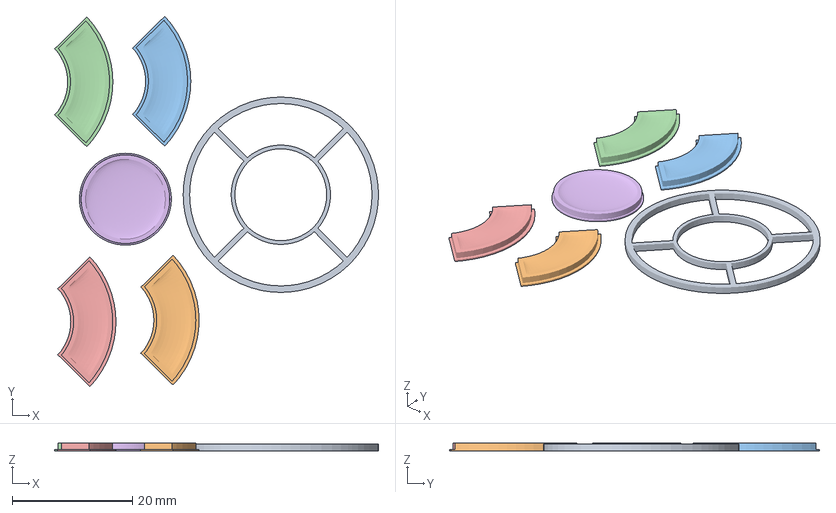
[picture p97: CAD file, 2025-07-07]
stl/dpadring.3mf
53.9 x 61.6 x 1.37 mm
dpadring.stl
dpadarrow.stl
dpadenter.stl
