MrDoritos/Wearable/stl/sh1107 inner.3mf

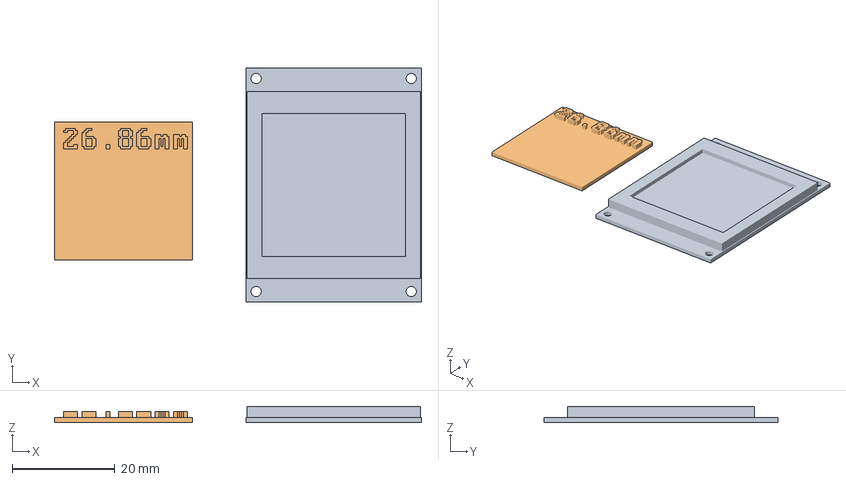
[picture p98: CAD file, 2025-07-07]
stl/sh1107 inner.3mf
71.5 x 45.5 x 3.16 mm
sh1107.stl
sh1107 inner.stl
