MrDoritos/Wearable/stl/sh1107.stl

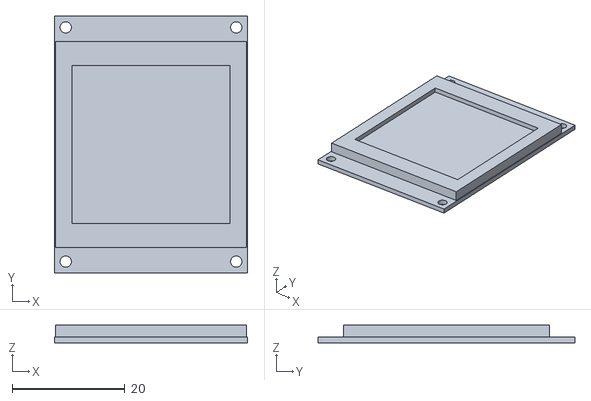
[picture p99: CAD file, 2025-07-07]
stl/sh1107.stl
34.2 x 45.5 x 3.16
