MrDoritos/Wearable/stl/dpad.stl

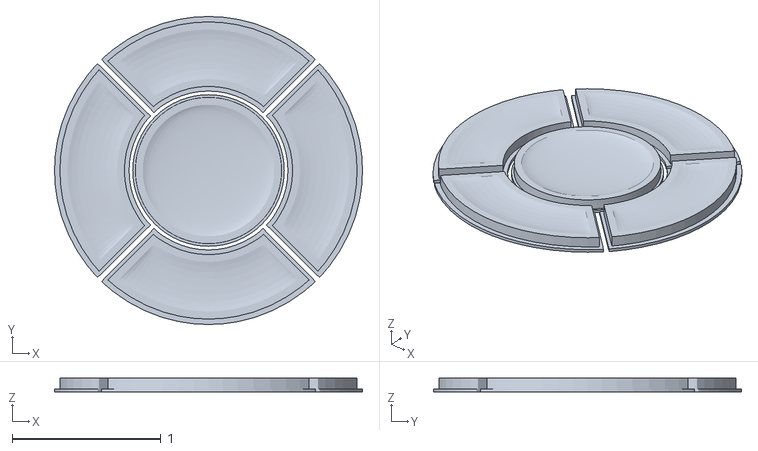
[picture p100: CAD file, 2025-07-06]
stl/dpad.stl
2.07 x 2.07 x 0.0911
