MrDoritos/Wearable/stl/GT-U7.stl

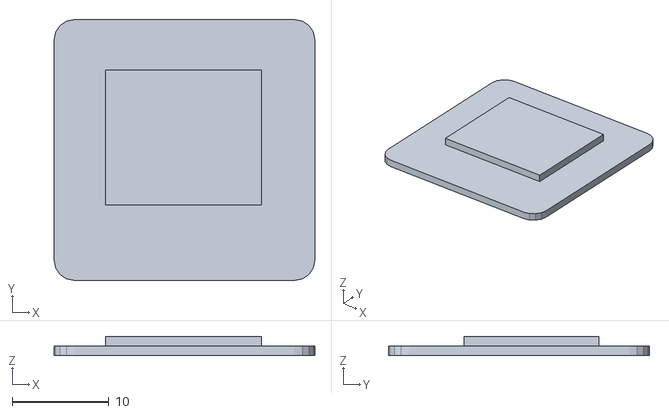
[picture p101: CAD file, 2025-06-28]
stl/GT-U7.stl
27.0 x 27.0 x 2.00
