MrDoritos/Wearable/stl/ADA254.stl

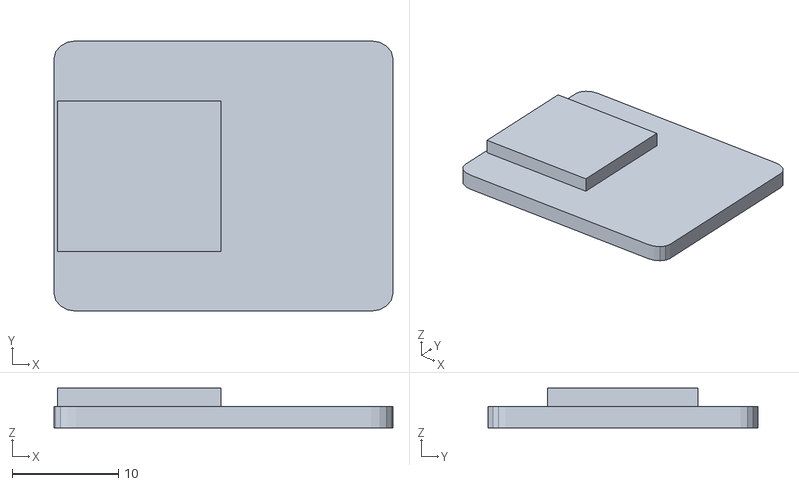
[picture p102: CAD file, 2025-06-28]
stl/ADA254.stl
31.8 x 25.4 x 3.75
