MrDoritos/Wearable/stl/ESP8266.stl

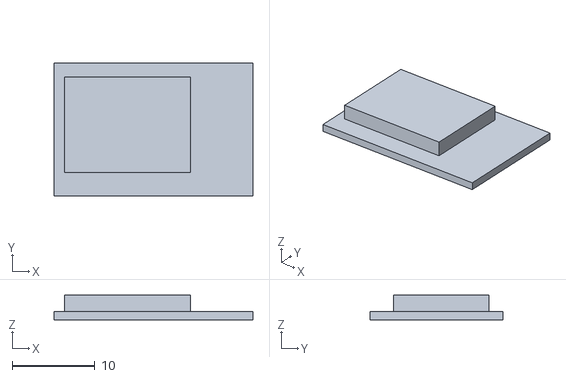
[picture p103: CAD file, 2025-06-28]
stl/ESP8266.stl
24.0 x 16.0 x 3.00
