MrDoritos/Wearable/stl/Lipo 1200.stl

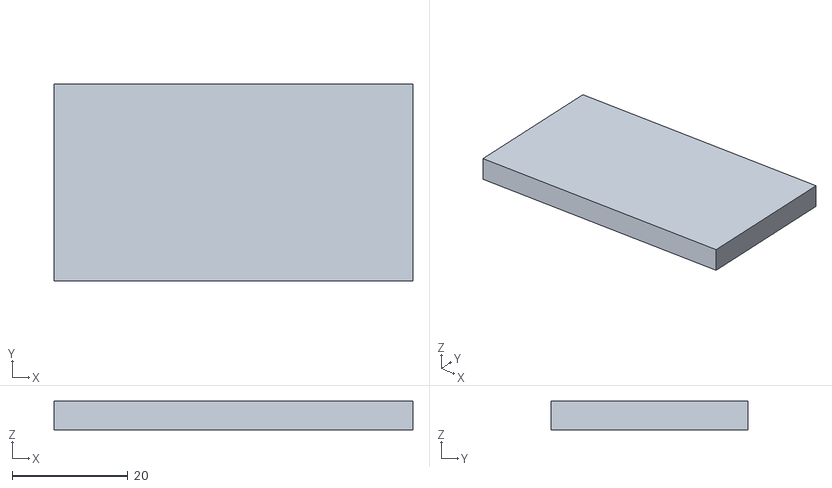
[picture p104: CAD file, 2025-06-28]
stl/Lipo 1200.stl
62.0 x 34.0 x 5.00
