MrDoritos/Wearable/stl/AHT21.stl

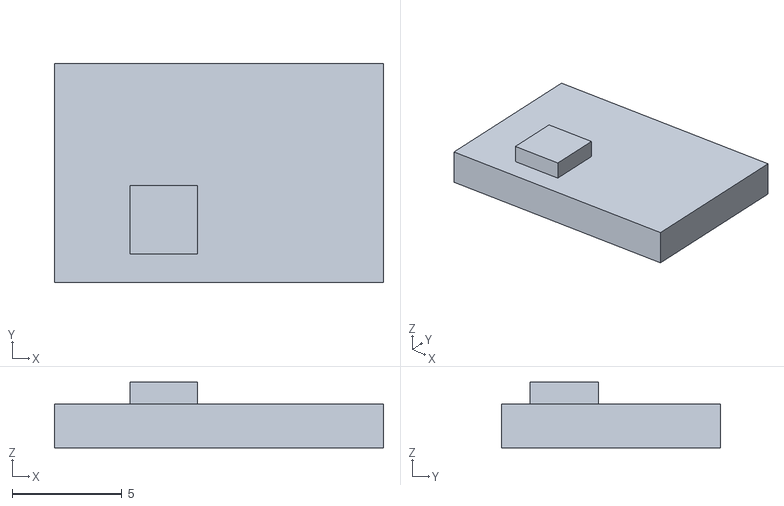
[picture p105: CAD file, 2025-06-28]
stl/AHT21.stl
15.0 x 10.0 x 3.00
