MrDoritos/Wearable/stl/ADXL345.stl

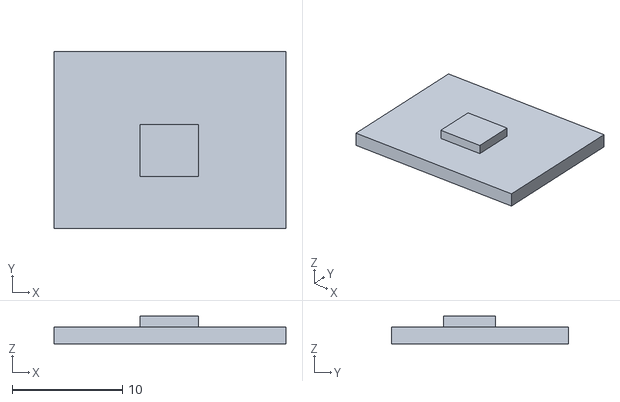
[picture p106: CAD file, 2025-06-28]
stl/ADXL345.stl
21.0 x 16.0 x 2.50
