MrDoritos/Wearable/stl/BME280.stl

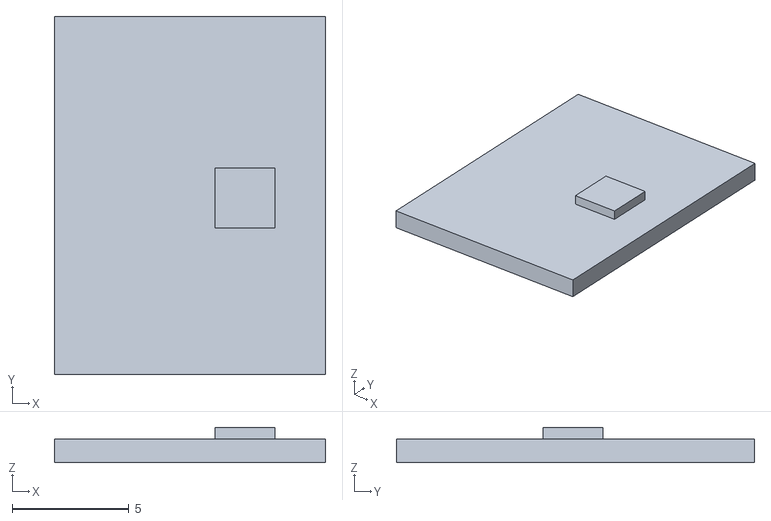
[picture p107: CAD file, 2025-06-28]
stl/BME280.stl
11.6 x 15.3 x 1.50
