MrDoritos/Wearable/layout2_wiring.png

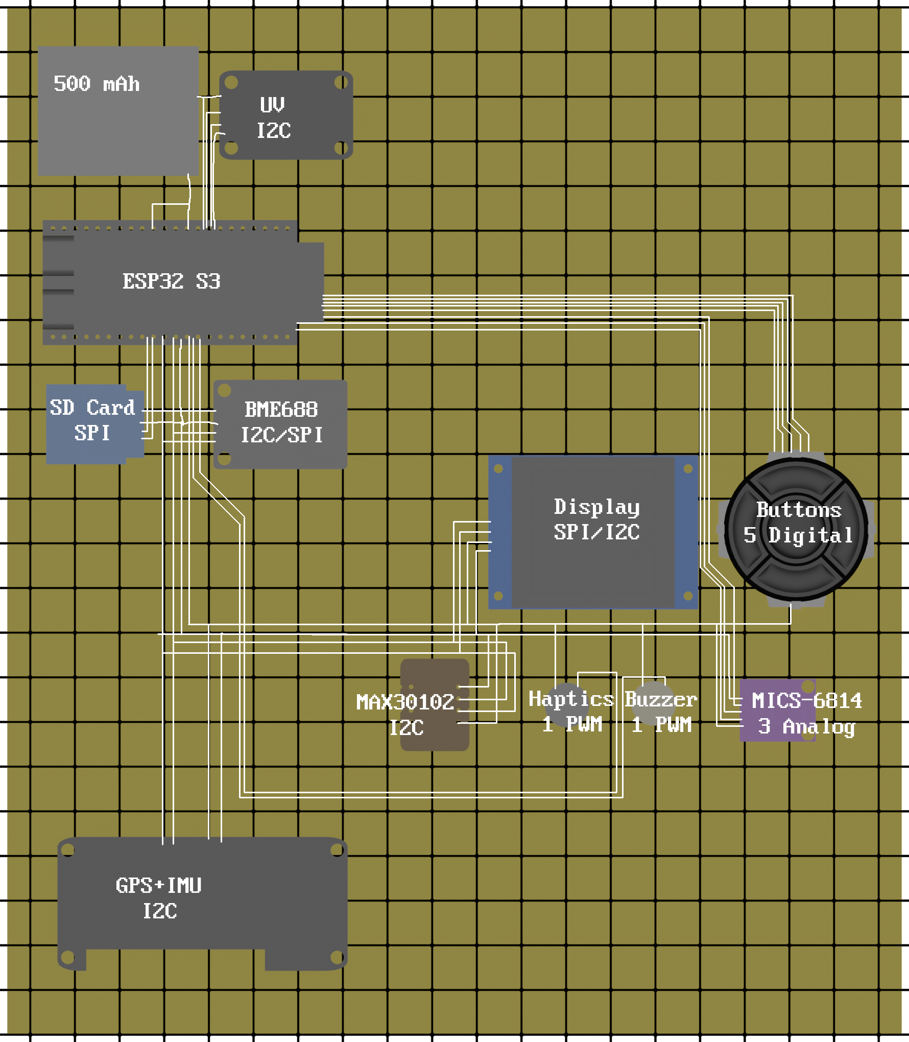
layout2_wiring.png
