MrDoritos/Wearable/Wearable/src/emulator/consolebuffer.h

#pragma once

#include "framebuffer.h"
#include "console.h"

#include <string.h>
#include <inttypes.h>

namespace wbl {

struct Display {
    inline int clearDisplay(const pixel &c=0);
    inline int init();
};

struct ConsoleBuffer : public FramebufferT<StaticbufferT<128,128,1>>, public Display {
    using Frame = FramebufferT<StaticbufferT<128,128,1>>;

    static constexpr const char* blockMap = " \0▘\0▝\0▀\0▖\0▌\0▞\0▛\0▗\0▚\0▐\0▜\0▄\0▙\0▟\0█\0";
    static constexpr const char* blockMap2w = "  \0▀ \0 ▀\0▀▀\0▄ \0█ \0▄▀\0█▀\0 ▄\0▀▄\0 █\0▀█\0▄▄\0█▄\0▄█\0██\0";
    static constexpr const char *blockMapAscii = " \0`\0'\0^\0,\0[\0/\0<\0.\0\\\0]\0>\0_\0L\0J\0#\0";
    static constexpr const char *blockMapAscii2w = "  \0^ \0 ^\0^^\0v \0$ \0v^\0$^\0 v\0^v\0 $\0^$\0vv\0$v\0v$\0$$\0";

    inline int init() {return 0;}

    inline fb blockToNum(const fb &x, const fb &y, const fb &xn, const fb &yn) {
        fb num = 0;
        const fb mask = (1 << this->BPP) - 1;
        const fb tot = 1 << (xn * yn);
        for (int j = y, k = 0; j < y + yn; j++)
            for (int i = x; i < x + xn; i++, k+=this->BPP)
                num |= (getPixel(i, j) & mask) << k;
        return num & (tot - 1);
    }

    template<typename BLOCKSRC>
    inline void flushBlocks(const BLOCKSRC blockmap, const int &w=1, const int &stride_x=2, const int &stride_y=2);

    inline int flush();

    inline int clearDisplay() {
        this->clear();
        return this->flush();
    }

    inline int setDisplay(const uint8_t &flags = 0) { return 0; }

    inline int setOrientation(const uint8_t &flags = 0) { return 0; }

    inline int setContrast(const uint8_t &flags = 0) { return 0; }

    inline int setState(const bool &on = true) { return 0; }

    inline int setInverted(const bool &invert = false) { return 0; }
};

template<typename BLOCKSRC>
void ConsoleBuffer::flushBlocks(const BLOCKSRC _blockMap, const int &w, const int &stride_x, const int &stride_y) {
    const int cwidth = console::getConsoleWidth(), cheight = console::getConsoleHeight();
    const int clength = cwidth * cheight;
    const int mapLength = (1 << (stride_x * stride_y));
    const int blength = clength * 4 * w;
    const char *blockMap = (const char*)_blockMap;

    int mapOffsets[mapLength][2];
    for (int i = 0, j = 0, k = 0, l = 0; i < mapLength; 
        l = strlen(blockMap + j), j += l + 1, mapOffsets[i][0] = k, mapOffsets[i][1] = l, k = j, i++);

    char ch_buffer[blength];
    int offset2 = 0, _offset = 0;

    memset(ch_buffer, ' ', blength);

    for (int sy = 0, cy = 0; sy < this->HEIGHT && cy < cheight; sy+=stride_y, cy++) {
        for (int sx = 0, cx = 0; sx < this->WIDTH && cx < (cwidth & -2); sx+=stride_x, cx+=w) {
            const int num = blockToNum(sx, sy, stride_x, stride_y);
            const char *ch = &blockMap[mapOffsets[num][0]];
            const int l = mapOffsets[num][1];
            const int offset = cy * cwidth + cx;

            for (int i = 0; i < l; i++)
                ch_buffer[i + offset + offset2] = ch[i];

            offset2 += (l-w);
            _offset = offset + offset2;
        }
    }

    ch_buffer[_offset+w] = '\0';
    console::clear();
    console::write(0, 0, ch_buffer);
}

int ConsoleBuffer::flush() {
    flushBlocks(blockMap2w, 2);
    return 0;
}

using DisplayBuffer = ConsoleBuffer;

}
