MrDoritos/Wearable/Wearable/src/user_inputs.h

#pragma once

#include "types.h"
#include "esp_types.h"
#include "esp_system.h"

#include <stdio.h>

namespace wbl {

struct Dpad {
    enum States : ub {
        NONE = 0,
        PRESSED = 1,
        HELD = 2,
        RELEASED = 4,
        NUMSTATES=3,
    };

    struct Button {
        volatile States state{NONE};

        constexpr inline void rising_edge() {
            if (!(state & States::HELD) || !state)
                state = (States)(state | States::PRESSED);
        }

        constexpr inline void falling_edge() {
            if (state & ~States::RELEASED)
                state = (States)(state | States::RELEASED);
        }

        /*
            @brief Call after using values

            Call after using values, like after distributing UI events for user input

            Required to reset pressed and released events, as well 
                as provide the ability to detect held buttons.
        */
        constexpr inline void update() {
            if (state & States::PRESSED) {
                state = (States)(state ^ States::PRESSED);
                state = (States)(state | States::HELD);
            }
            if (state & States::RELEASED)
                state = States::NONE;
        }

        constexpr inline bool is_pressed() const {
            return state & States::PRESSED;
        }

        constexpr inline bool is_released() const {
            return state & States::RELEASED;
        }

        constexpr inline bool is_held() const {
            return state & States::HELD;
        }
    };

    const ub button_count = 5;

    Button enter, up, right, down, left;

    Button *buttons = &enter;

    esp_err_t init();
    ~Dpad();

    static constexpr const char *names[] = {
        "Enter", "Up", "Right", "Down", "Left"
    };
    static constexpr const char *states[] = {
        "Pressed", "Held", "Released"
    };
    
    constexpr inline void print_states() const {
        for (int i = 0; i < States::NUMSTATES; i++) {
            const int buflen = 50;
            char buf[buflen]={};
            int offset = 0;
            bool v = false;
            offset += snprintf(buf+offset, buflen-offset, "%s: ", states[i]);
            for (int j = 0; j < button_count; j++) {
                if (buttons[j].state & (1<<i)) {
                    offset += snprintf(buf+offset, buflen-offset, "%s%s", (v?", ":""), names[j]);
                    v = true;
                }
            }
            if (v) {
                offset += snprintf(buf+offset, buflen-offset, "\n");
                fwrite(buf, 1, offset, stdout);
            }
        }
        fflush(stdout);
    }

    constexpr inline void update() {
        for (int i = 0; i < button_count; i++)
            buttons[i].update();
    }

    constexpr inline bool any_state() const {
        for (int i = 0; i < button_count; i++)
            if (buttons[i].state)
                return true;
        return false;
    }

    constexpr inline bool any(const States &state) const {
        for (int i = 0; i < button_count; i++)
            if (buttons[i].state & state)
                return true;
        return false;
    }

    constexpr inline void set_states(const States &state) {
        for (int i = 0; i < button_count; i++)
            buttons[i].state = state;
    }
};

extern Dpad dpad;

}
