MrDoritos/Wearable/Wearable/src/peripheral/gps_imu.cpp

#include "gps_imu.h"
#include "imu.h"

#include "LSM6DSLSensor.h"

namespace wbl {

I2C lsm6dsl(I2C_BUS_1, I2C_LSM6DSL_ADDR, 1000, I2C_LSM6DSL_FREQ, 40000);
I2C lis3mdl(I2C_BUS_1, I2C_LIS3MDL_ADDR, 1000, I2C_LIS3MDL_FREQ, 40000);
I2C bme388(I2C_BUS_1, I2C_BME388_ADDR, 1000, I2C_BME388_FREQ, 40000);
GPSIMU gpsimu;
LSM6DSLSensor s_lsm6dsl((TwoWire*)1, I2C_LSM6DSL_ADDR);
uint8_t pedometer_state = 0;

static constexpr const char *TAG = "wbl::gps_imu.cpp";

esp_err_t GPSIMU::init() {
    ESP_RETURN_ON_ERROR(lsm6dsl.init(), TAG, "lsm6dsl init failed");
    ESP_RETURN_ON_ERROR(lis3mdl.init(), TAG, "lis3mdl init failed");
    ESP_RETURN_ON_ERROR(bme388.init(), TAG, "bme388 init failed");

    if (s_lsm6dsl.begin()) {
        return 1;
    }

    if (s_lsm6dsl.Enable_X()) return 1;
    if (s_lsm6dsl.Enable_G()) return 1;

    if (s_lsm6dsl.Set_X_ODR(12.5) || s_lsm6dsl.Set_G_ODR(12.5) || s_lsm6dsl.Set_X_FS(4.0))
        return 1;

    s_lsm6dsl.WriteReg(0x73, 39);
    s_lsm6dsl.WriteReg(0x74, 49);
    s_lsm6dsl.WriteReg(0x75, 38);
    /*
    s_lsm6dsl.WriteReg(0x2D, 2017&0xff);
    s_lsm6dsl.WriteReg(0x2E, 2017>>8);
    s_lsm6dsl.WriteReg(0x2F, 455&0xff);
    s_lsm6dsl.WriteReg(0x30, 455>>8);
    */
    enablePedometer();

    return ESP_OK;
}

AxisData GPSIMU::getGyroscope() {
    int32_t axis[3];
    s_lsm6dsl.Get_G_Axes(axis);
    return AxisData(axis[0] * 0.001, axis[1] * 0.001, axis[2] * 0.001);
}

AxisData GPSIMU::getAccelerometer() {
    int32_t axis[3];
    s_lsm6dsl.Get_X_Axes(axis);
    return AxisData(axis[0] * 0.001, axis[1] * 0.001, axis[2] * 0.001);
}

esp_err_t GPSIMU::setPedometerState(uint8_t state) {
    if (state == pedometer_state)
        return ESP_OK;

    if (state) {
        ESP_RETURN_ON_ERROR(enablePedometer(), TAG, "enable pedometer");
    } else {
        ESP_RETURN_ON_ERROR(disablePedometer(), TAG, "disable pedometer");
    }

    pedometer_state = state;

    return ESP_OK;
}

uint8_t GPSIMU::getPedometerState() {
    return pedometer_state;
}

esp_err_t GPSIMU::enablePedometer() {
    s_lsm6dsl.Enable_Pedometer();

    pedometer_state = 1;

    return ESP_OK;
}

esp_err_t GPSIMU::disablePedometer() {
    s_lsm6dsl.Disable_Pedometer();

    pedometer_state = 0;

    return ESP_OK;
}

esp_err_t GPSIMU::resetPedometer() {
    s_lsm6dsl.Reset_Step_Counter();

    return ESP_OK;
}

uint16_t GPSIMU::getPedometer() {
    uint16_t ret;
    if (pedometer_state && !s_lsm6dsl.Get_Step_Counter(&ret))
        return ret;

    return 0;
}

}
