MrDoritos/Wearable/Wearable/src/ui/sprites.h

#pragma once

#include "font.h"
#include "texture.h"

#define THEROCK

namespace wbl {
namespace Sprites {

using DisplayTexture = TextureT<DisplayBuffer>;
extern DisplayTexture display;

using FontBuffer = FramebufferT<StaticbufferT<256, 256, 2>>;
using FontTexture = TextureT<FontBuffer>;
using FontProvider = MonospaceFontProviderT<FontTexture, 6, 12, 0, 0, char, 42, 14>;
using FontSprite = FontProvider::FontSprite;
extern const FontProvider font asm("_binary_dosjpn_bin_start");

using AtlasBuffer = FramebufferT<StaticbufferT<256, 256, 2>>;
using Atlas = AtlasT<AtlasBuffer>;
using AtlasFontSprite = FontSpriteT<Atlas::Sprite, char>;

extern const Atlas atlas asm("_binary_textures_bin_start");

#ifdef THEROCK

using RockTexture = TextureT<FramebufferT<StaticbufferT<128, 128, 2>>>;
extern const RockTexture therock asm("_binary_therock_bin_start");

#endif

#define TX(name, x, y, w, h) static constexpr Atlas::Sprite name = atlas.getSprite(x, y, w, h);
#define FT(x,y,w,h) AtlasFontSprite(atlas, x, y, w, h, 1, 1)
#define FT35(x,y) FT(x,y,3,5)


TX(BATTERY_4x8, 0, 10, 4, 8)
TX(BATTERY_5x10, 0, 18, 5, 10)
TX(BATTERY_13x6, 5, 11, 13, 6)
TX(BATTERY_5x10_PAD, 5, 18, 6, 11)

#define BATTERY BATTERY_5x10

TX(HEART_LARGE, 20, 12, 11, 11)
TX(HEART_SMALL, 32, 13, 9, 8)

#define HEART HEART_SMALL

TX(VERT_BAR, 25, 23, 2, 11)
TX(VERT_BAR_NONE, 27, 23, 2, 11)
TX(SLASH, 31, 23, 4, 11)
TX(DUMMY, 0, 0, 0, 0)

TX(LOCK_ICON, 29, 37, 8, 11)

static constexpr const AtlasFontSprite GLYPHS_NUM_3x5[] = {
    FT35(0,0),
    FT35(3,0),
    FT35(6,0),
    FT35(9,0),
    FT35(12,0),
    FT35(15,0),
    FT35(18,0),
    FT35(21,0),
    FT35(24,0),
    FT35(27,0),
};

static constexpr const AtlasFontSprite GLYPHS_ALPHA_3x5[] = {
    FT35(71,0), // A
    FT35(75,0), // B
    FT35(79,0), // C
    FT35(83,0), // D
    FT35(87,0), // E
    FT35(91,0), // F
    FT35(95,0), // G
    FT35(99,0), // H
    FT35(103,0), // I
    FT35(107,0), // J
    FT35(111,0), // K
    FT35(115,0), // L
    FT(175,0,5,5), // M
    FT(181,0,4,5), // N
    FT35(127,0), // O
    FT35(131,0), // P
    FT35(135,0), // Q
    FT35(139,0), // R
    FT35(143,0), // S
    FT35(147,0), // T
    FT35(151,0), // U
    FT35(155,0), // V
    FT(186,0,5,5), // W
    FT35(163,0), // X
    FT35(167,0), // Y
    FT35(171,0), // Z
};

#define F35Baseline 35
#define F35(x) FT35(x, F35Baseline)
#define F35W(x, w, h) FT(x, F35Baseline, w, h)

static constexpr const AtlasFontSprite GLYPHS_ALPHA_LOWER_3x5[] = {
    F35(71), // a
    F35(75), // b
    F35W(79, 2, 5), // c
    F35(83), // d
    F35(87), // e
    F35W(91, 2, 5), // f
    F35(95), // g
    F35(99), // h
    F35W(103, 1, 5), // i
    F35W(107, 2, 5), // j
    F35(111), // k
    F35W(115, 2, 5), // l
    F35W(119, 5, 5), // m
    F35(125), // n
    F35(129), // o
    F35(133), // p
    F35(137), // q
    F35W(141, 2, 5), // r
    F35W(145, 2, 5), // s
    F35(149), // t
    F35(153), // u
    F35(157), // v
    F35W(161, 5, 5), // w
    F35(167), // x
    F35(171), // y
    F35W(175, 2, 5), // z
};

#undef F35Baseline
#undef F35
#undef F35W

static constexpr const AtlasFontSprite GLYPHS_SPECIAL_3x5[] = {
    //FT35(0,5), // %
    FT35(191,0), // SPACE
    FT(196,0,1,5), // !
    FT35(198,0), // "
    FT(202,0,5,5), // #
    FT35(207,0), // $

    FT35(210,0), // %
    FT35(213,0), // &
    FT(217,0,1,5), // '
    FT35(219,0), // (
    FT35(223,0), // )

    FT35(227,0), // *
    FT35(231,0), // +
    FT(235,0,2,5), // ,
    FT35(238,0), // -
    FT(242,0,1,5), // .

    FT35(244,0), // /
    FT(248,0,1,5), // :
    FT(250,0,2,5), // ;
    FT35(71,30), // >
    FT35(75,30), // =

    FT35(79,30), // <
    FT35(83,30), // ?
    FT(87,30,4,5), // @
    FT(92,30,2,5), // [
    FT35(95,30), // BACKSLASH

    FT(99,30,2,5), // ]
    FT35(102,30), // ^
    FT35(106,30), // _
    FT(110,30,2,5), // `
    FT(114,30,2,5), // {

    FT(117,30,1,5), // |
    FT(119,30,2,5), // }
    FT(122,30,4,5), // ~
};

#undef TX
#undef FT
#undef FT35

/*
template<typename Derived, typename Fallback, typename AtlasSourceT = typename Derived::Atlas, typename FontSpriteT = typename Derived::FontSprite, typename FontSpriteFallbackT = typename Fallback::FontSprite, typename CharT = char>
struct GlyphFontProviderT : public Derived, public Fallback {
    using Char = CharT;

    inline constexpr FontSprite getCharacter(const CharT &character) const {
        const FontSprite *sprite = Derived::getCharacter(character);
        if (sprite)
            return sprite;
        
        return Fallback::getCharacter(character);
    }
};

struct MinifontProvider : public GlyphFontProviderT<MinifontProvider, FontProvider, FontTexture, AtlasFontSprite> {
    using GlyphBase = GlyphFontProviderT<MinifontProvider, FontProvider>;
    using FontSprite = typename FontProvider::FontSprite;
    using Char = GlyphBase::Char;

    inline constexpr FontSprite *getCharacter(const Char &character) const {
        if (character >= '0' && character <= '9')
            return &GLYPHS_NUM_3x5[character-'0'];
    }

}
*/

struct MinifontProvider : public TextureT<FramebufferT<Memorybuffer<const pixel>>> {
    constexpr MinifontProvider():TextureT(256, 256, 2, &atlas.buffer[0]){}

    using Memory = FramebufferT<Memorybuffer>;
    using MemTex = TextureT<Memory>;
    using MemAtl = AtlasT<Memory, MemTex>;
    using Sprite = typename MemAtl::Sprite;
    using Font = FontSpriteT<Sprite, char>;

    template<typename T>
    inline constexpr Font convSrc(const T &sprite) const {
        //return Font(*((const MemTex*)sprite.src), sprite.font_width, sprite.font_height, sprite.advance_x, sprite.advance_y);
        Font font = (Font&)sprite;
        const_cast<const MemTex*&>(font.src) = this;
        return font;
    }

    inline constexpr Font getCharacter(const char &character) const {
        if (character >= '0' && character <= '9')
            return convSrc(GLYPHS_NUM_3x5[character-'0']);
        if (character >= 'a' && character <= 'z')
            return convSrc(GLYPHS_ALPHA_LOWER_3x5[character-'a']);
        if (character >= 'A' && character <= 'Z')
            return convSrc(GLYPHS_ALPHA_3x5[character-'A']);
        if (character >= ' ' && character <= '/')
            return convSrc(GLYPHS_SPECIAL_3x5[character-' ']);
        if (character >= ':' && character <= '@')
            return convSrc(GLYPHS_SPECIAL_3x5[character-':'+16]);
        if (character >= '[' && character <= '`')
            return convSrc(GLYPHS_SPECIAL_3x5[character-'['+23]);
        if (character >= '{' && character <= '~')
            return convSrc(GLYPHS_SPECIAL_3x5[character-'{'+29]);
        return convSrc(font.getCharacter(character));
    }
};

const MinifontProvider minifont;

}
}
