MrDoritos/Wearable/Wearable/src/ui/ui_texturewriter.h

#pragma once

#include "config.h"
#include "ui.h"

namespace wbl {
namespace UI {

template<typename ElementT = ElementBaseT<Sprites::DisplayTexture>>
struct TextureWriterT {
    ElementT &ref;
    bool wrap, clip_x, clip_y;
    Size size; // inline x, offset y, inline height
    const Size boundary;

    constexpr TextureWriterT(ElementT &ref, const Size &boundary):
        ref(ref),
        wrap(ref.wrap & WRAP),
        clip_x(ref.overflow.x & HIDDEN),
        clip_y(ref.overflow.y & HIDDEN),
        size(boundary.getOffset(), Length(0)),
        boundary(boundary) {}
        
    constexpr TextureWriterT(ElementT &ref, const Origin &pos):
        TextureWriterT(ref, Size(pos, ref.getLength())) {}
    constexpr TextureWriterT(ElementT &ref):TextureWriterT(ref, ref.getOffset()) {}
    constexpr TextureWriterT(ElementT *ref, const Origin &pos):TextureWriterT(*ref,pos) {}
    constexpr TextureWriterT(ElementT *ref, const Size &boundary):TextureWriterT(*ref,boundary) {}
    constexpr TextureWriterT(ElementT *ref):TextureWriterT(*ref) {}
        
    inline void setOffsetY(const uu &y) {
        size.y = y + boundary.y;
    }

    inline void setOffsetX(const uu &x) {
        size.x = x + boundary.x;
    }

    inline void add_break() {
        size.y += size.height;
        size.x = boundary.x;
        size.height = 0;
    }

    bool add_length(const Length &length, Origin &pos) {
        if (length.width + size.x > boundary.width + boundary.x) {
            if (wrap)
                add_break();
            else
            if (clip_x)
                return false;
        }

        if (clip_y && length.height + size.y > boundary.height + boundary.y)
            return false;

        if (size.height < length.height)
            size.height = length.height;
        
        pos = size;

        size.x += length.width;

        return true;
    }

    template<typename FontProvider, typename Format, int buflen=100, typename ...Args>
    void printf(const FontProvider &font, Format format, const Args&...args) {
        char buf[buflen];
        snprintf(buf, buflen, format, args...);
        text(font, buf);
    }

    template<typename Sprite>
    void sprite(const Sprite &sp) {
        Origin pos;
        if (!add_length(sp, pos))
            return;
        ref.buffer.putSprite(sp, pos);
    }

    template<typename Glyph>
    void glyph(const Glyph &gl) {
        Origin pos;
        const Length glyph_size(
            gl.font_width + gl.advance_x,
            gl.font_height + gl.advance_y  
        );
        if (!add_length(glyph_size, pos))
            return;
        ref.buffer.putSprite(gl, pos);
    }

    template<typename Sprite>
    void sprite(const Sprite *sp, const int &num_sp=1) {
        for (int i = 0; i < num_sp; i++)
            sprite(*sp);
    }

    template<typename Sprite>
    void sprites(const Sprite &sp) {
        sprite(sp);
    }

    template<typename Sprite, typename ...Args>
    void sprites(const Sprite &sp, const Args&...args) {
        sprite(sp);
        sprites(args...);
    }

    template<typename FontProvider>
    void text(const FontProvider &font, const char *txt) {
        const int length = strlen(txt);

        for (int i = 0; i < length; i++) {
            const char ch = txt[i];

            if (ch == '\n') {
                add_break();
                continue;
            }

            glyph(font.getCharacter(ch));
        }
    }

    template<typename Callback>
    void text_callback(const char *txt, Callback callback) {
        const int length = strlen(txt);

        for (int i = 0; i < length; i++) {
            const char &ch = txt[i];

            if (ch == '\n') {
                add_break();
                continue;
            }

            callback(ch);
        }
    }

    template<typename FontProvider>
    void subscript(const FontProvider &font, const char *txt) {
        text_callback(
        txt, 
        [&](const char &ch) {
            const auto &gl = font.getCharacter(ch);
            const Length glyph_size(
                gl.font_width + gl.advance_x,
                gl.font_height + gl.advance_y
            );
            Origin pos;
            if (!add_length(glyph_size, pos))
                return;
            pos.y += (size.height - (glyph_size.height * 0.5));
            ref.buffer.putSprite(gl, pos);
        });
    }

    template<typename FontProvider>
    void print_timer_time(const FontProvider &font, const int64_t &time, const int64_t &div = 1000) {
        int64_t t_millis = time / div;
        int millis = t_millis % 1000;
        int seconds = (t_millis / 1000) % 60;
        int mins = (t_millis / 60000) % 60;
        int hrs = (t_millis / (60*60*1000));

        if (hrs) printf(font, "%i:", hrs);
        if (mins) printf(font, "%02i:", mins);
        printf(font, "%02i", seconds);
        size.x++;
        printf(Sprites::minifont, "%03i", millis);
    }

    template<typename Base, typename value_type = typename Base::value_type, typename FontProvider, int buflen = 100>
    void print_value(const FontProvider &font, const value_type &value) {
        char buf[buflen];
        Base::template printf<value_type>(buf, buflen, value);
        text(font, buf);
    }
};

}
}
